ties1887/Mesh-radio-Halow-LoRa/images/345634.jpeg

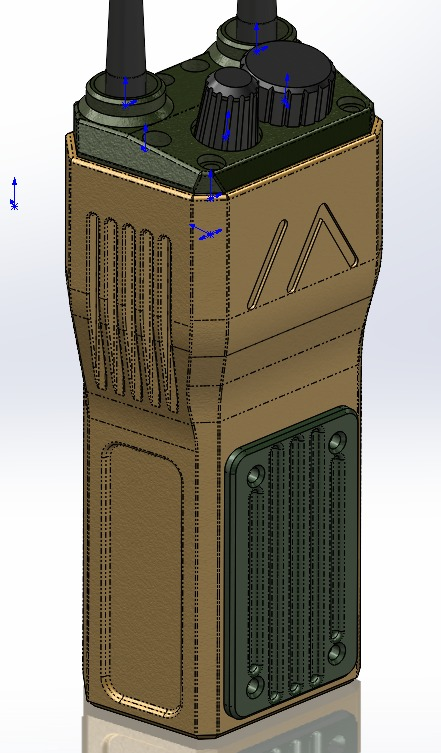
images/345634.jpeg
