ties1887/Mesh-radio-Halow-LoRa/images/2345235.jpeg

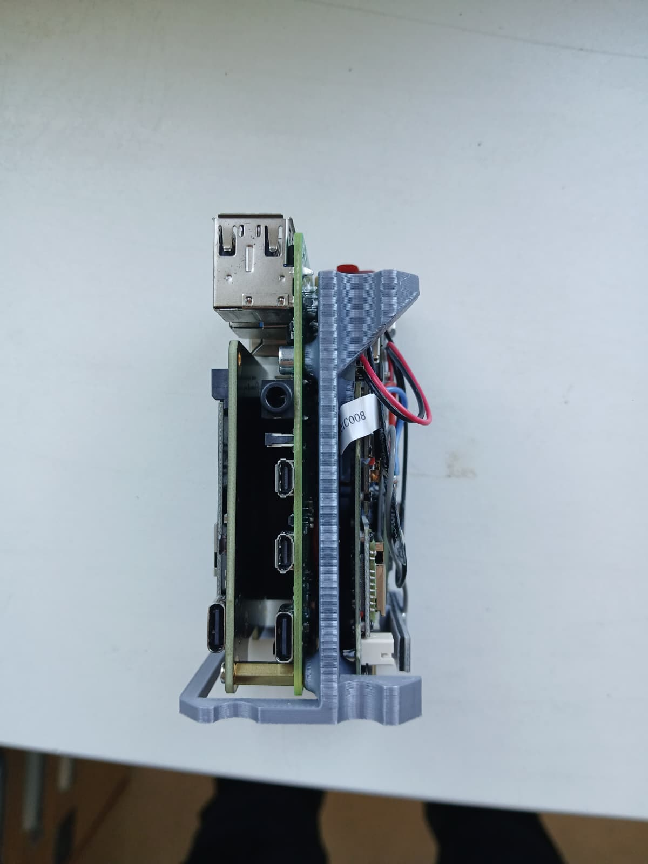
images/2345235.jpeg
