ties1887/Mesh-radio-Halow-LoRa/images/7345634.jpeg

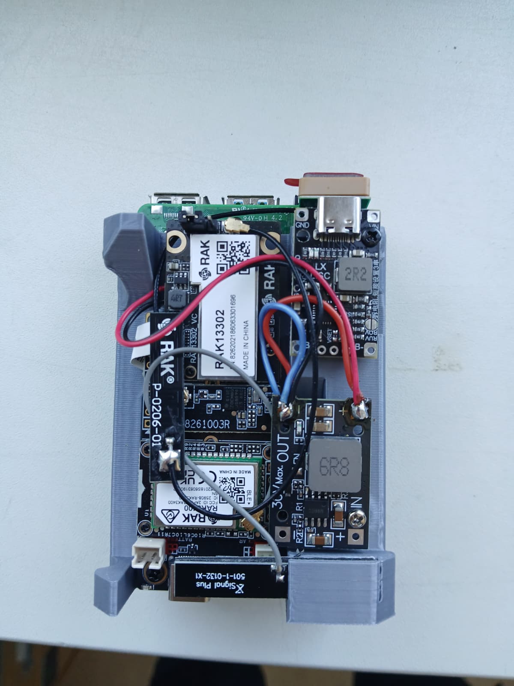
images/7345634.jpeg
