ties1887/Mesh-radio-Halow-LoRa/images/23452345.png

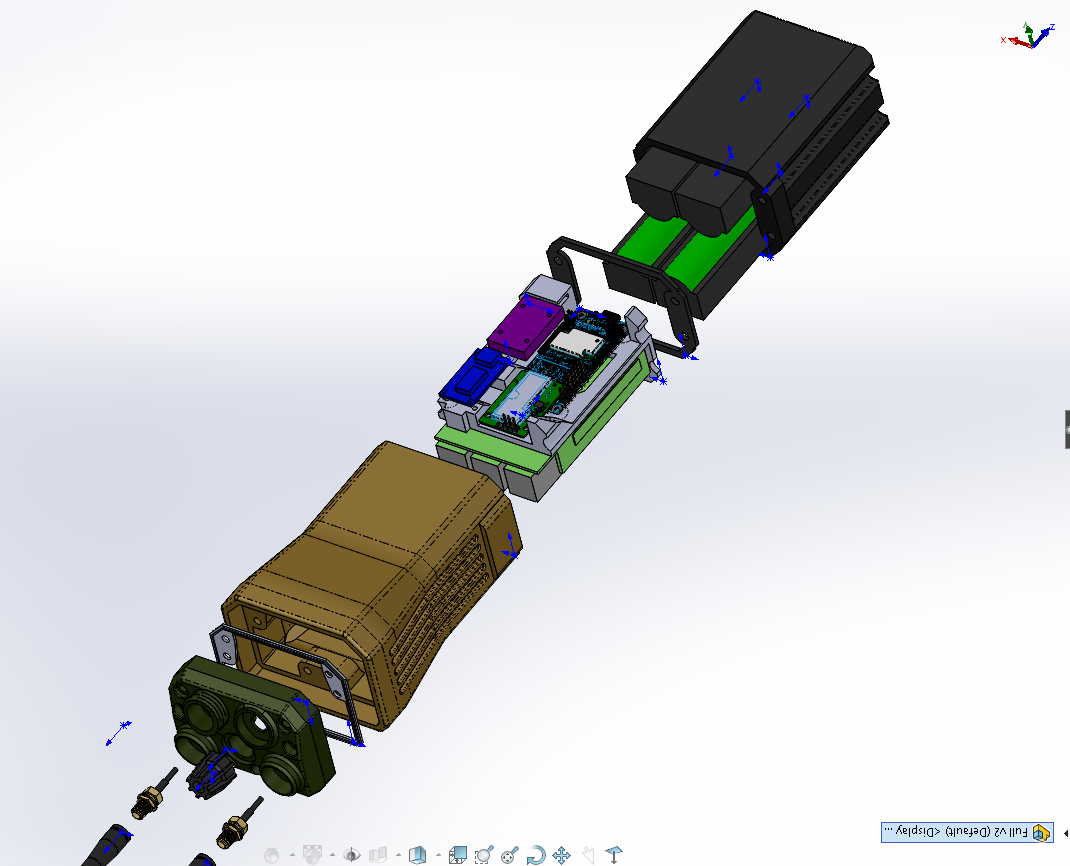
images/23452345.png
