ties1887/Mesh-radio-Halow-LoRa/images/45674567.jpeg

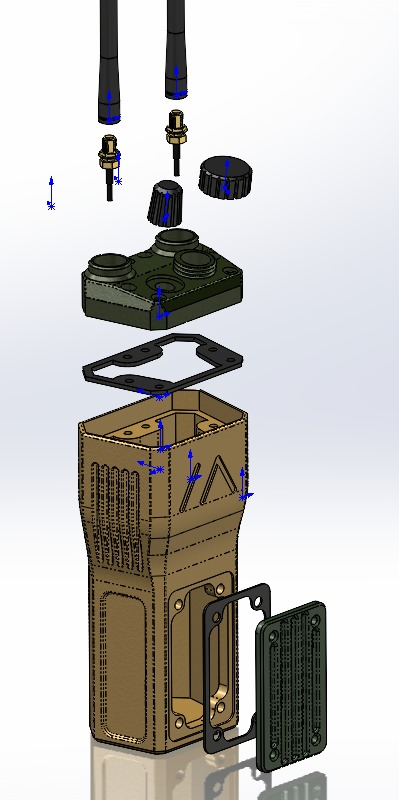
images/45674567.jpeg
