ties1887/Mesh-radio-Halow-LoRa/images/645737645.jpeg

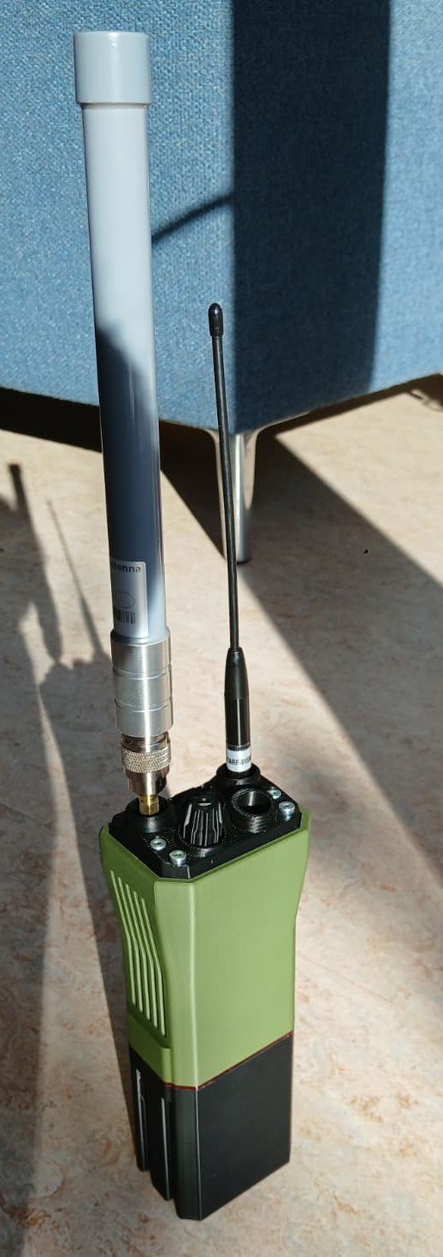
images/645737645.jpeg
