ties1887/Mesh-radio-Halow-LoRa/images/654745745.jpeg

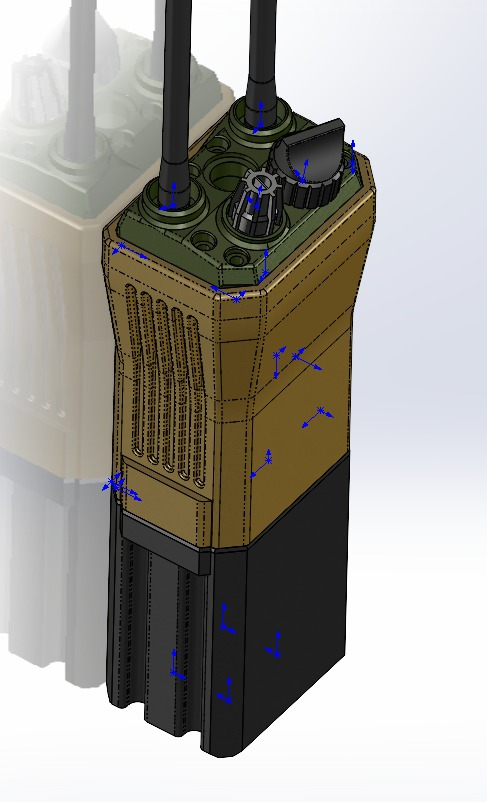
images/654745745.jpeg
