ties1887/Mesh-radio-Halow-LoRa/images/765474657.png

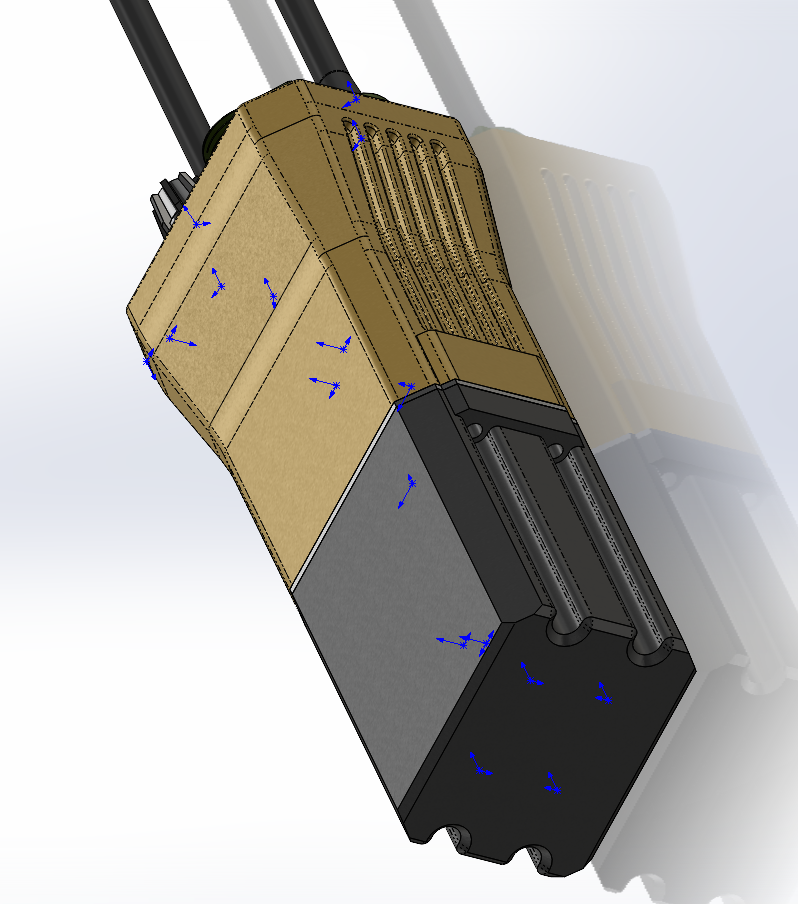
images/765474657.png
