ties1887/Mesh-radio-Halow-LoRa/images/2436436325.png

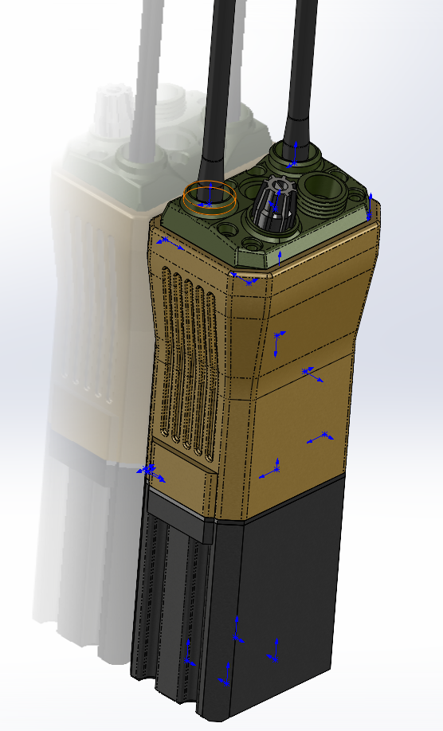
images/2436436325.png
