ties1887/Mesh-radio-Halow-LoRa/images/3456345634.jpeg

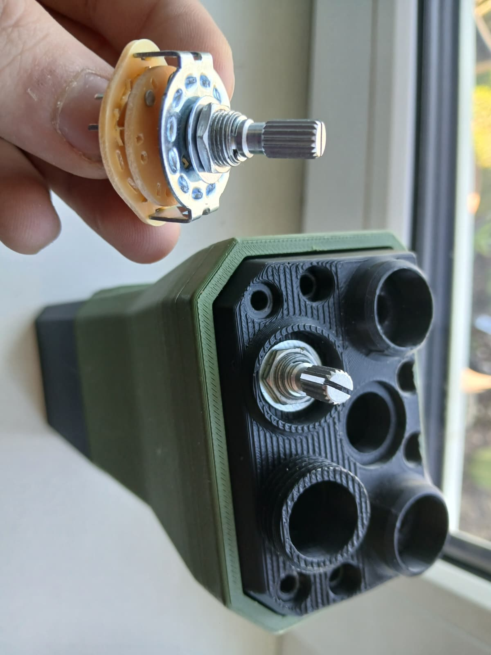
images/3456345634.jpeg
