ties1887/Mesh-radio-Halow-LoRa/images/3456346346.png

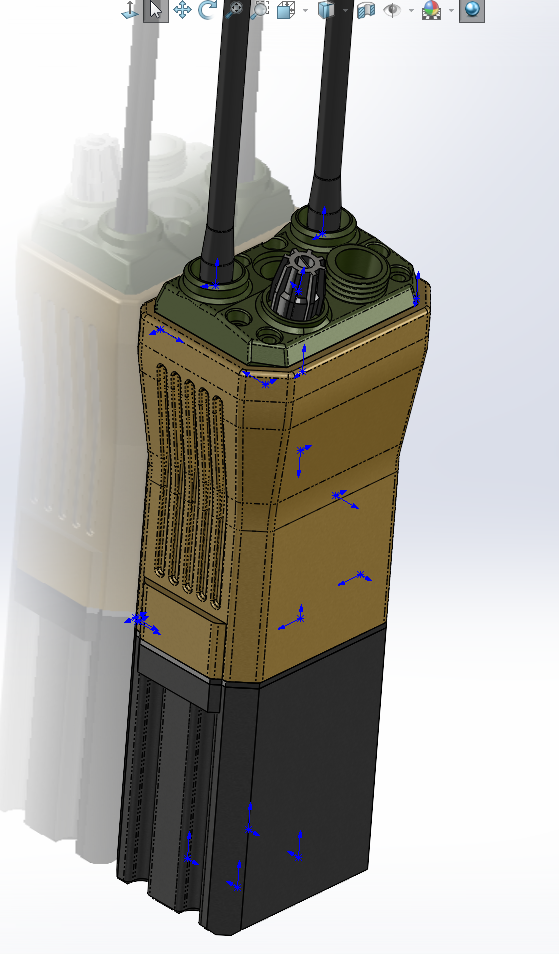
images/3456346346.png
