ties1887/Mesh-radio-Halow-LoRa/images/3456765437.png

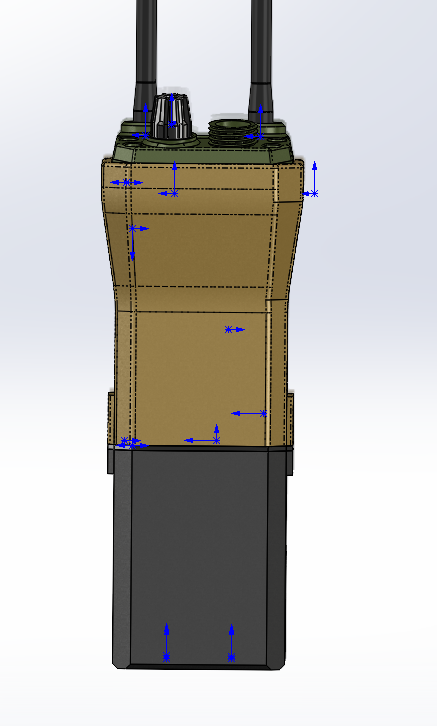
images/3456765437.png
