ties1887/Mesh-radio-Halow-LoRa/images/4567457457.jpeg

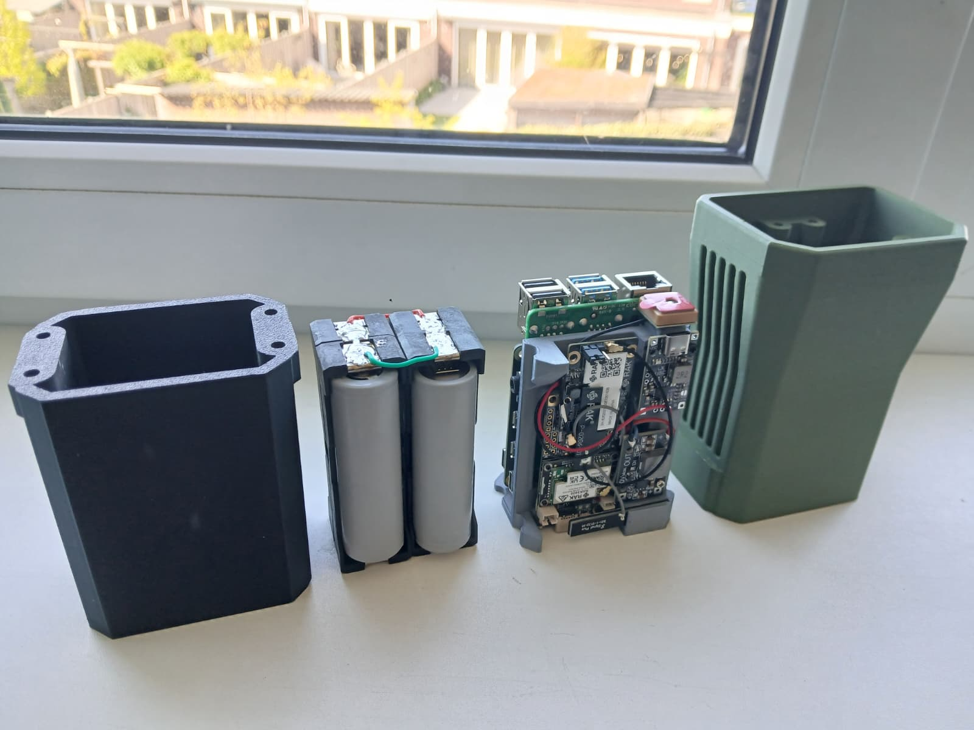
images/4567457457.jpeg
