ties1887/Mesh-radio-Halow-LoRa/images/7686587568.jpeg

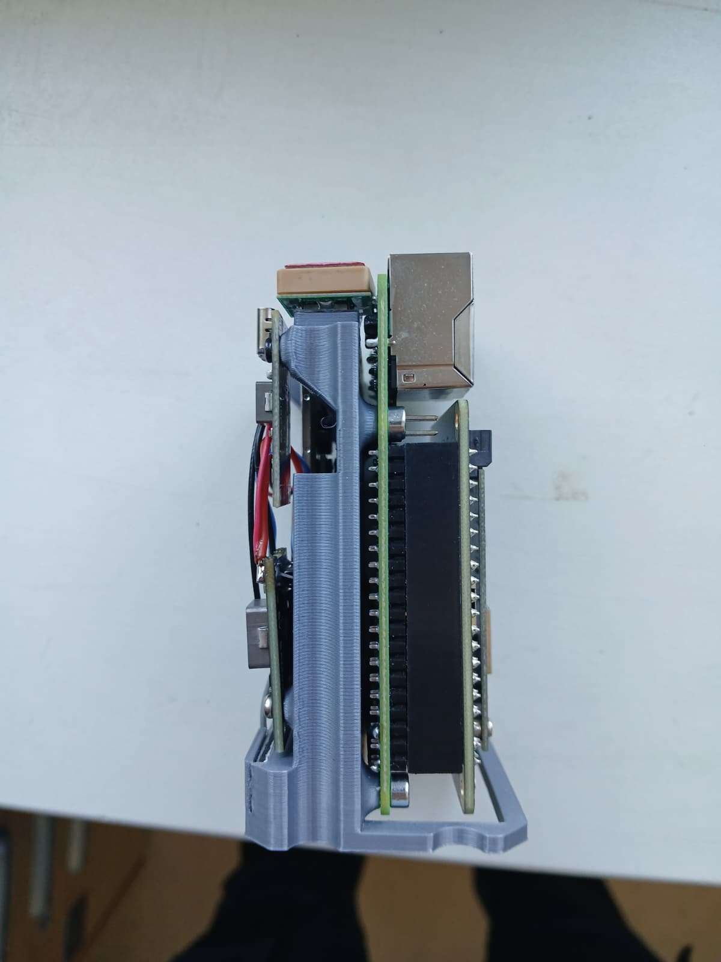
images/7686587568.jpeg
