ties1887/Mesh-radio-Halow-LoRa/images/45674567457.jpeg

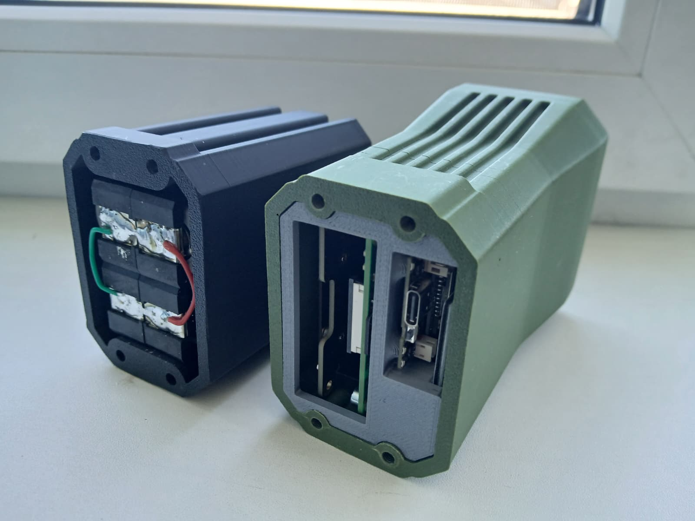
images/45674567457.jpeg
