ties1887/Mesh-radio-Halow-LoRa/images/45674567457.png

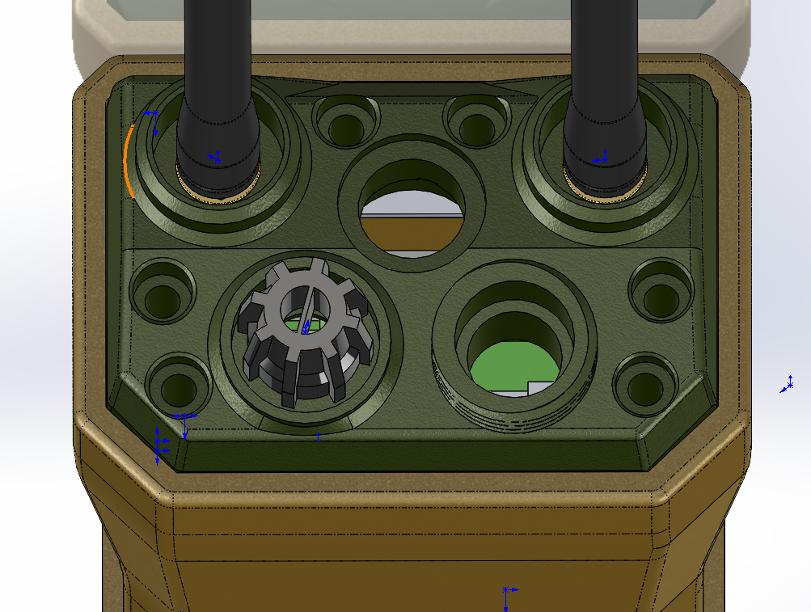
images/45674567457.png
