ties1887/Mesh-radio-Halow-LoRa/images/54674567457.jpeg

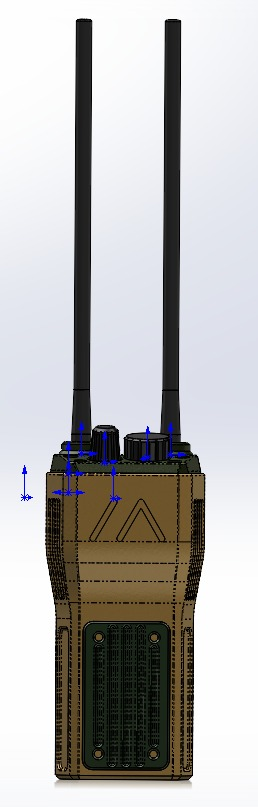
images/54674567457.jpeg
