ties1887/Mesh-radio-Halow-LoRa/images/64574567456.jpeg

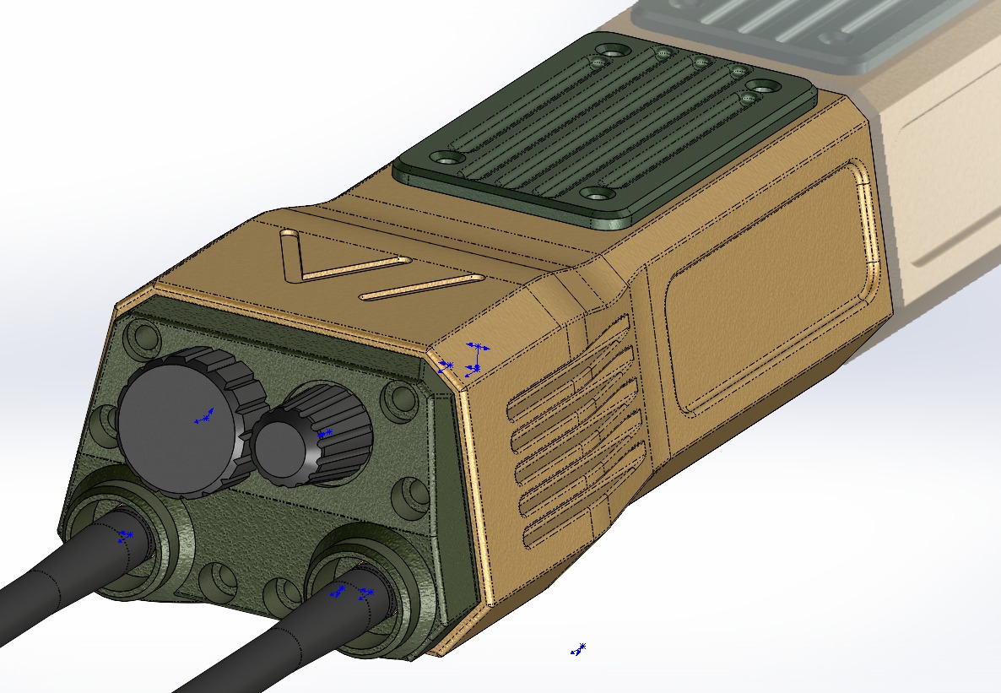
images/64574567456.jpeg
