ties1887/Mesh-radio-Halow-LoRa/images/75688568756.png

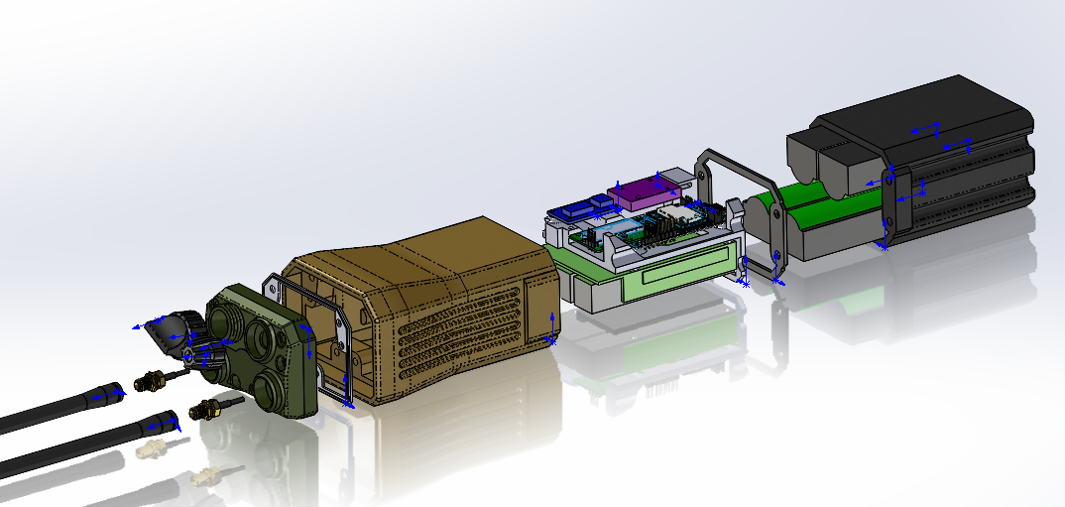
images/75688568756.png
