ties1887/Mesh-radio-Halow-LoRa/images/435634643643.jpeg

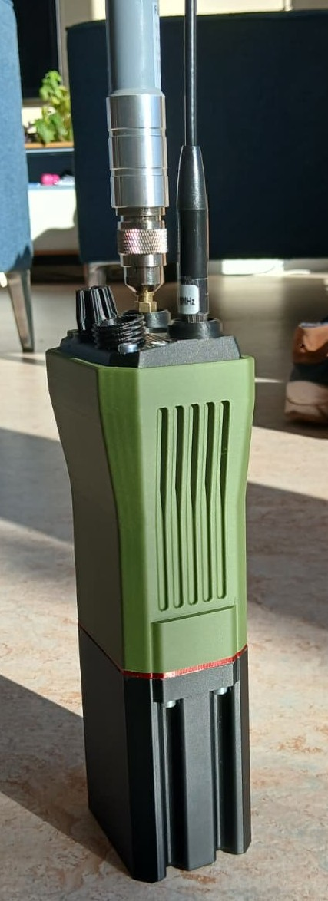
images/435634643643.jpeg
