ties1887/Mesh-radio-Halow-LoRa/images/567856785678.jpeg

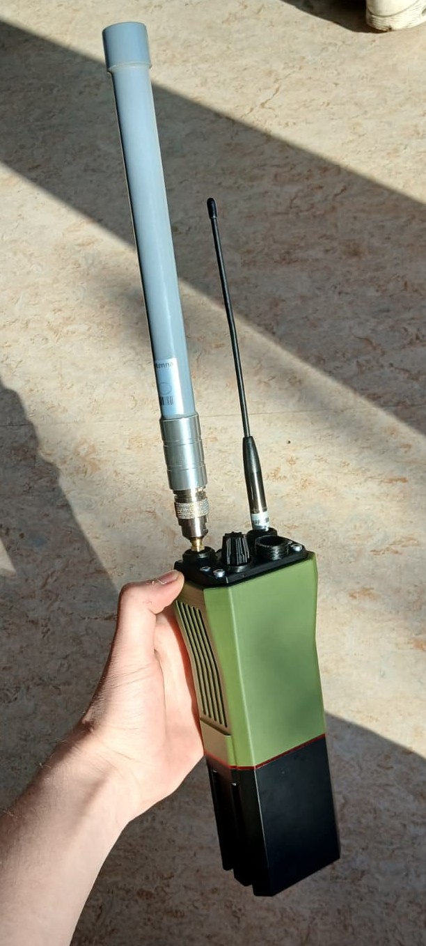
images/567856785678.jpeg
