ties1887/Mesh-radio-Halow-LoRa/images/765476547456.jpeg

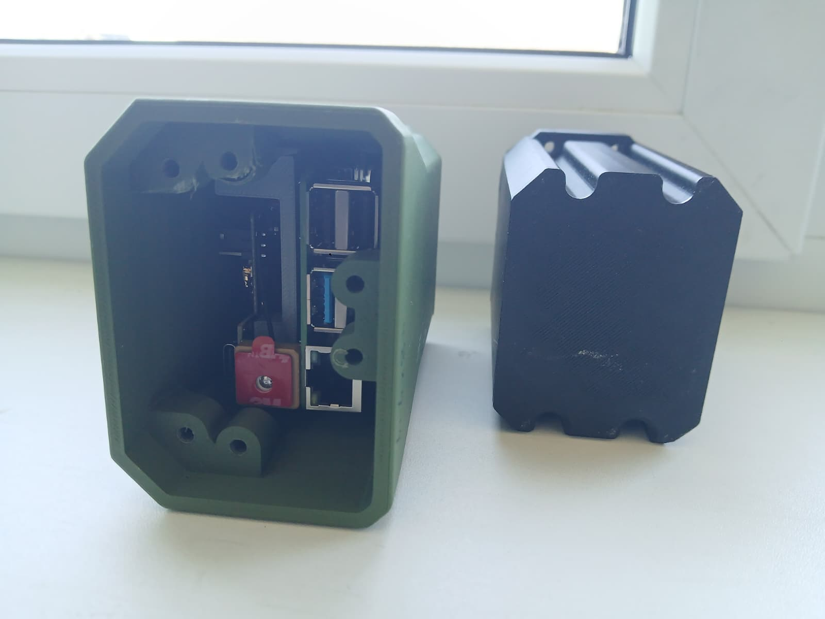
images/765476547456.jpeg
