ties1887/Mesh-radio-Halow-LoRa/images/3456345634634.jpeg

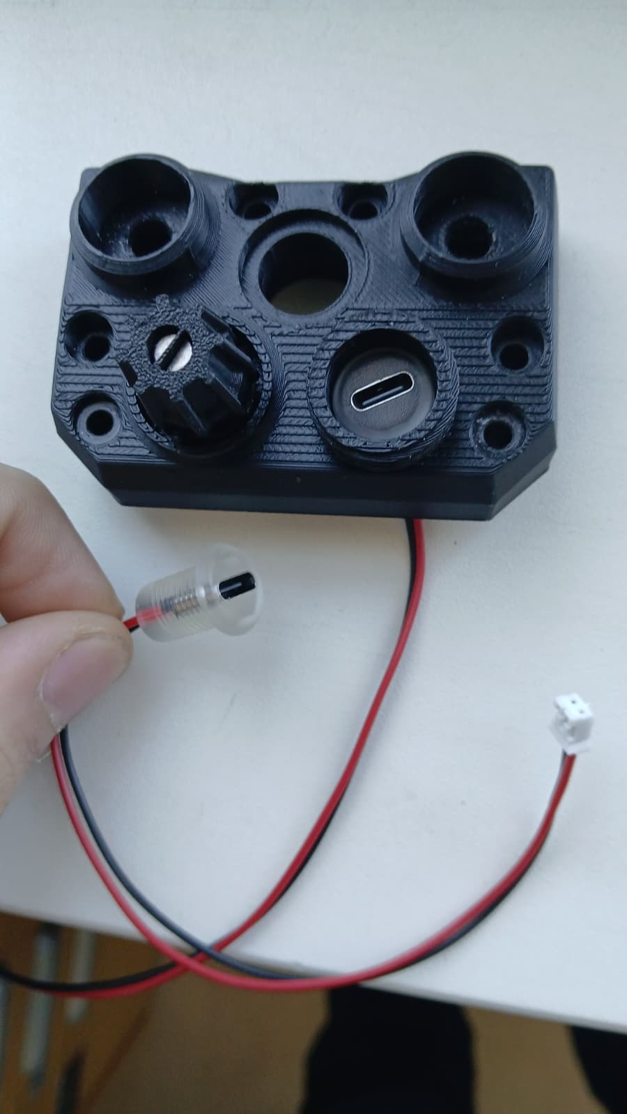
images/3456345634634.jpeg
