ties1887/Mesh-radio-Halow-LoRa/images/45674567435754.jpeg

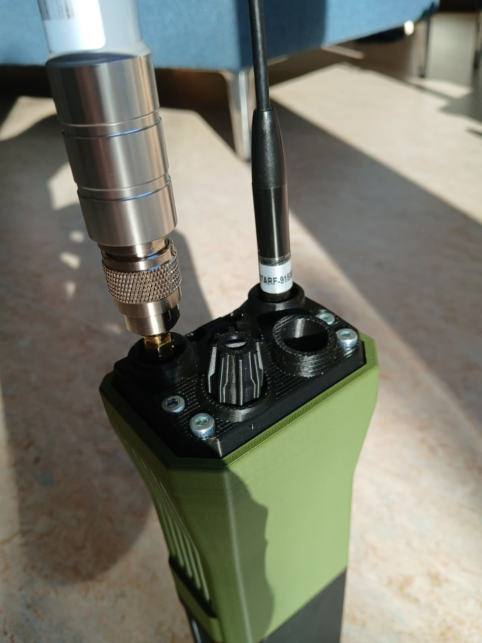
images/45674567435754.jpeg
