ties1887/Mesh-radio-Halow-LoRa/images/Schermafbeelding 2026-08-16 174457.png

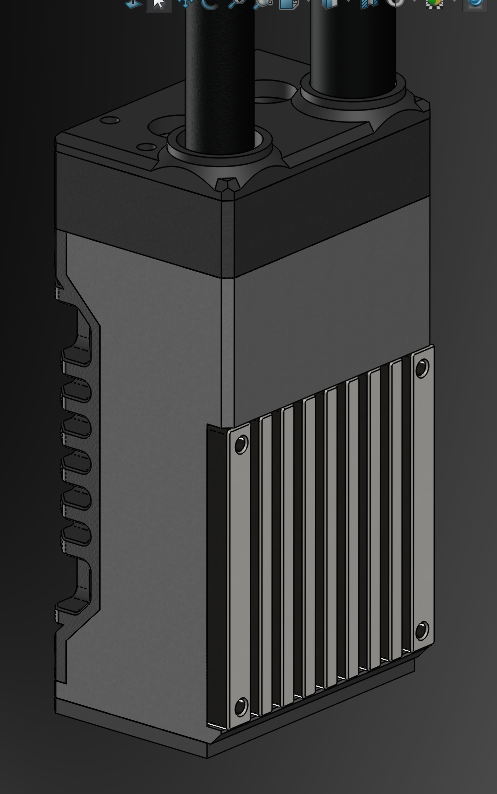
images/Schermafbeelding 2026-08-16 174457.png
