ties1887/Mesh-radio-Halow-LoRa/images/Schermafbeelding 2026-08-16 174508.png

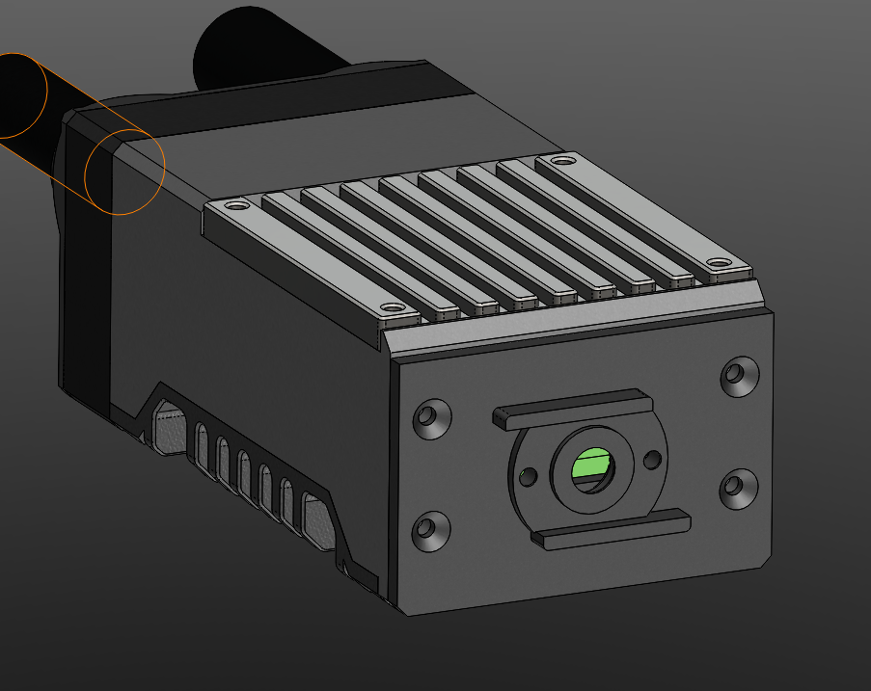
images/Schermafbeelding 2026-08-16 174508.png
