ties1887/Mesh-radio-Halow-LoRa/images/WhatsApp Image 2026-06-27 at 20.04.40.jpeg

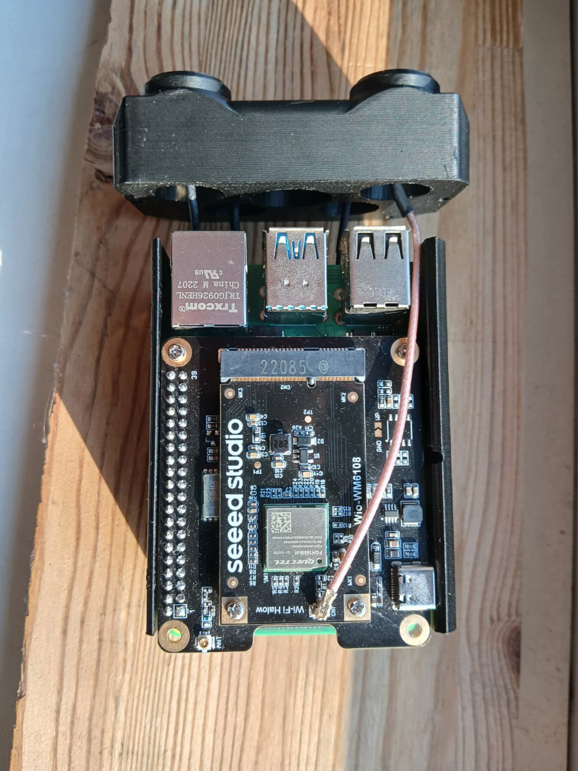
images/WhatsApp Image 2026-06-27 at 20.04.40.jpeg
