ties1887/Mesh-radio-Halow-LoRa/Twist-Lock-Battery-Pack/STL/Battery_Twist_Lock_Pack.SLDASM - Twist_Lock_Wing-1.STL

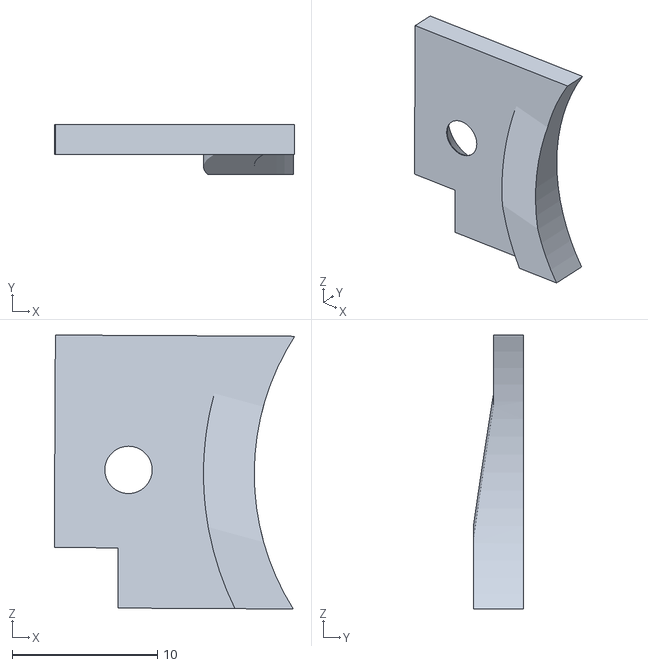
[picture p44: CAD file, 2026-08-21]
Twist-Lock-Battery-Pack/STL/Battery_Twist_Lock_Pack.SLDASM - Twist_Lock_Wing-1.STL
16.6 x 3.48 x 18.9
