ties1887/Mesh-radio-Halow-LoRa/Twist-Lock-Battery-Pack/STL/Battery_Twist_Lock_Pack.SLDASM - Battery_pin_Contact-1.STL

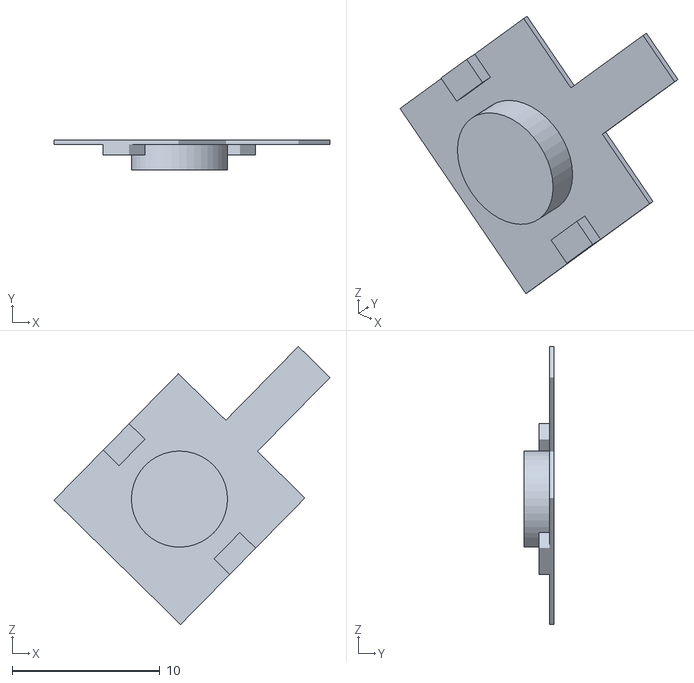
[picture p45: CAD file, 2026-08-21]
Twist-Lock-Battery-Pack/STL/Battery_Twist_Lock_Pack.SLDASM - Battery_pin_Contact-1.STL
18.7 x 2.00 x 18.8
