ties1887/Mesh-radio-Halow-LoRa/Twist-Lock-Battery-Pack/STL/Battery_Twist_Lock_Pack.SLDASM - Twist lock battery part V3-1.STL

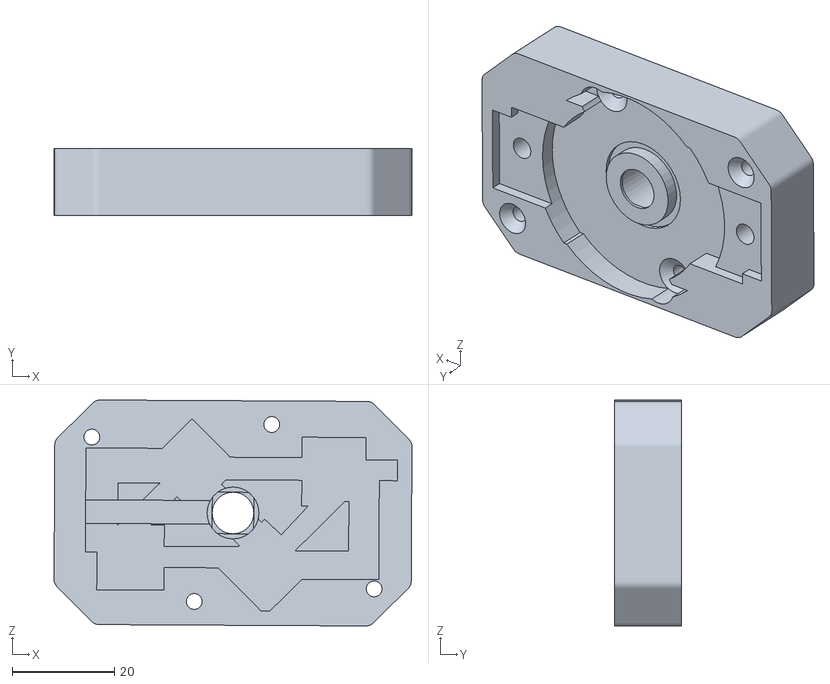
[picture p46: CAD file, 2026-08-21]
Twist-Lock-Battery-Pack/STL/Battery_Twist_Lock_Pack.SLDASM - Twist lock battery part V3-1.STL
70.1 x 13.1 x 44.3
