ties1887/Mesh-radio-Halow-LoRa/First-Generation-Builds/Standalone-Lunpid-enclosure/3MF/enclosure.3MF

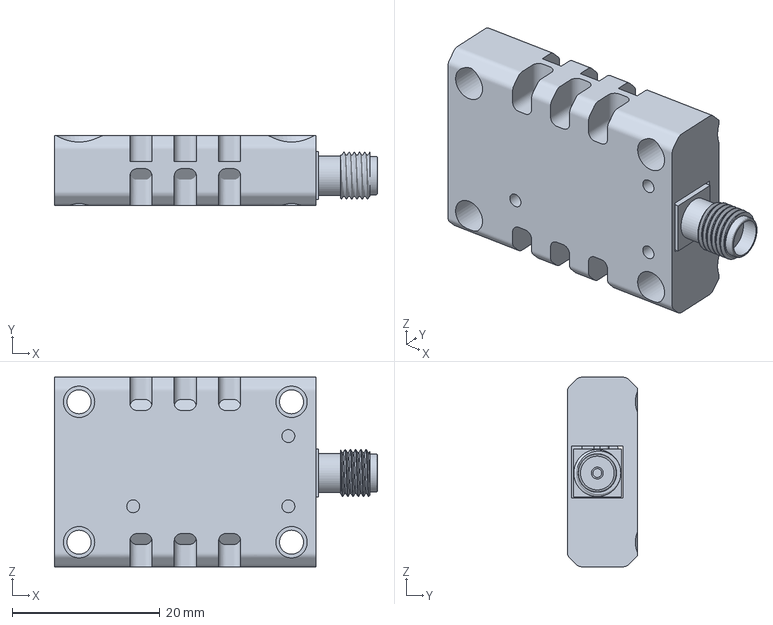
[picture p47: CAD file, 2026-07-13]
First-Generation-Builds/Standalone-Lunpid-enclosure/3MF/enclosure.3MF
43.7 x 9.50 x 25.6 mm
