ties1887/Mesh-radio-Halow-LoRa/First-Generation-Builds/Standalone-Lunpid-enclosure/Solidworks 2025/lunpid_longwave_v0.1.step

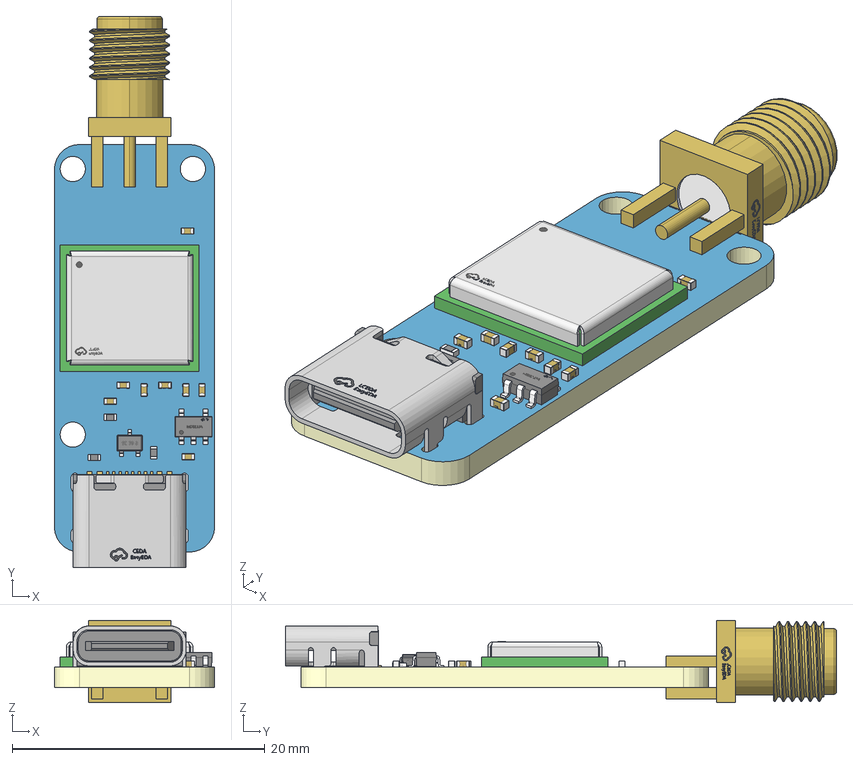
[picture p49: CAD file, 2026-07-13]
First-Generation-Builds/Standalone-Lunpid-enclosure/Solidworks 2025/lunpid_longwave_v0.1.step
12.7 x 43.6 x 6.50 mm
Board~8fiY
TopCopper~8fiY
BottomCopper~8fiY
TopSilkscreen~8fiY
BottomSilkscreen~8fiY
TopFpcStiffener~8fiY
BottomFpcStiffener~8fiY
SOT-23-5_L2.9-W1.6-P0.95-LS2.8-BL~SOT-23-5_ L2.9-W1.6-P0.95-LS2.8-BL~8fiY
R0402~C0402_L1.0-W0.5-H0.5~8fiY x 8
R0402~R0402_L1.0-W0.5-H0.4~8fiY x 3
SMA-SMD_BWSMA-KE-P001~SMA-TH_5P-L6.5-W6.5-H9.5_BWSMA-KE-P001~8fiY
SC-70-3_L2.0-W1.3-P0.65-LS2.1-BL~SC-70-3_L2.0-W1.3-P0.65-LS2.1-BL~8fiY
LGA-38_L11.0-W10.0-P1.00-TL~LGA-38_L11.0-W10.0-P1.00-TL~8fiY
USB-C-SMD_TYPE-C-6PIN-2MD-073~USB-C-SMD_TYPEC-304YDSW-ACP16~8fiY
