ties1887/Mesh-radio-Halow-LoRa/First-Generation-Builds/Standalone-Lunpid-enclosure/STEP/Top part.STEP

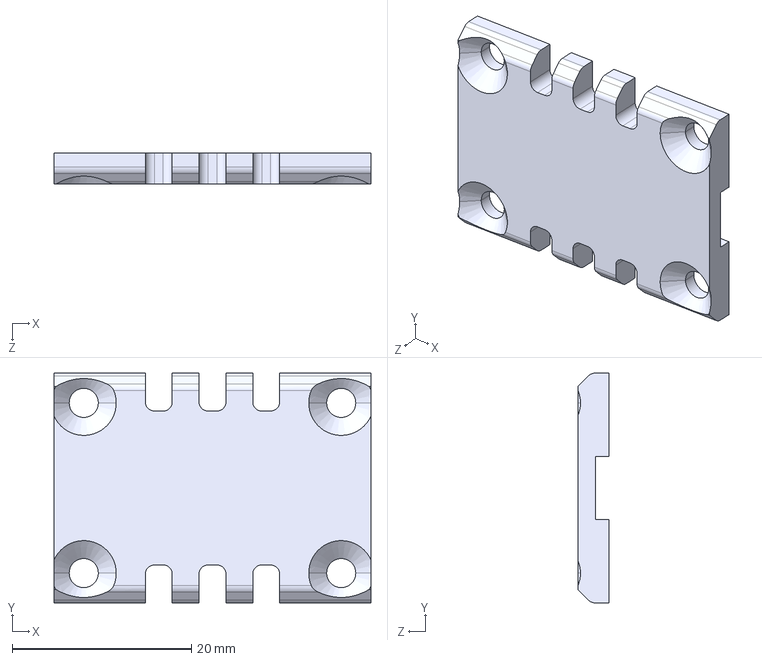
[picture p50: CAD file, 2026-07-13]
First-Generation-Builds/Standalone-Lunpid-enclosure/STEP/Top part.STEP
35.4 x 25.7 x 3.50 mm
