ties1887/Mesh-radio-Halow-LoRa/First-Generation-Builds/V2_30-5-2026/Solidworks 2023/base.SLDPRT

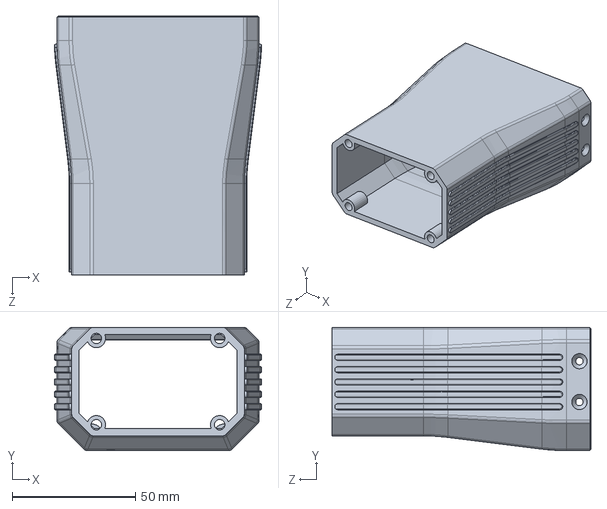
[picture p51: CAD file, 2026-05-30]
First-Generation-Builds/V2_30-5-2026/Solidworks 2023/base.SLDPRT
84.0 x 50.0 x 105.0 mm
