ties1887/Mesh-radio-Halow-LoRa/First-Generation-Builds/V2_30-5-2026/Solidworks 2025/middel part.SLDPRT

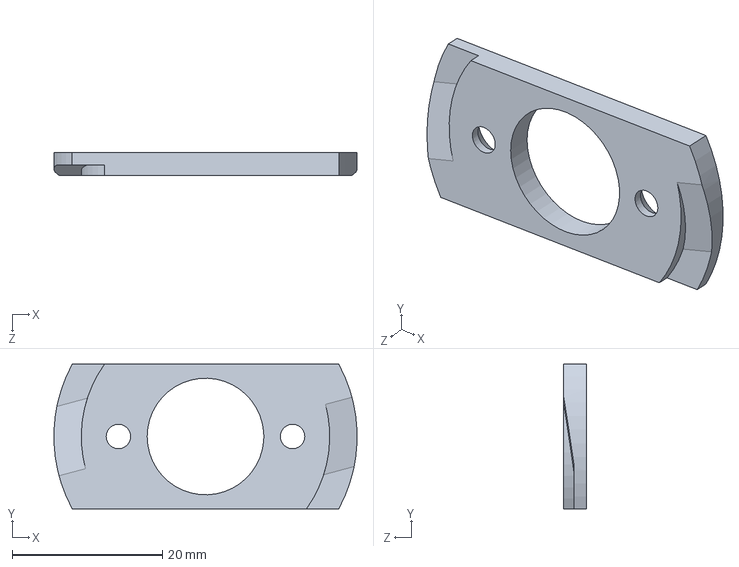
[picture p52: CAD file, 2026-05-30]
First-Generation-Builds/V2_30-5-2026/Solidworks 2025/middel part.SLDPRT
40.4 x 19.3 x 3.00 mm
