ties1887/Mesh-radio-Halow-LoRa/First-Generation-Builds/V2_30-5-2026/step/PCB frame.STEP

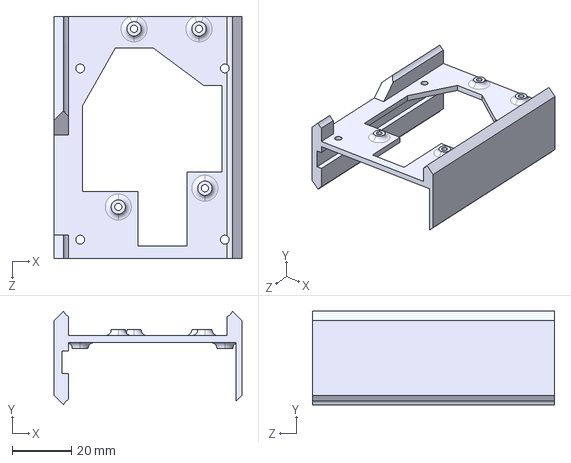
[picture p53: CAD file, 2026-05-30]
First-Generation-Builds/V2_30-5-2026/step/PCB frame.STEP
63.6 x 31.7 x 82.0 mm
