ties1887/Mesh-radio-Halow-LoRa/First-Generation-Builds/V2_30-5-2026/STL/Assem2 - top-1.STL

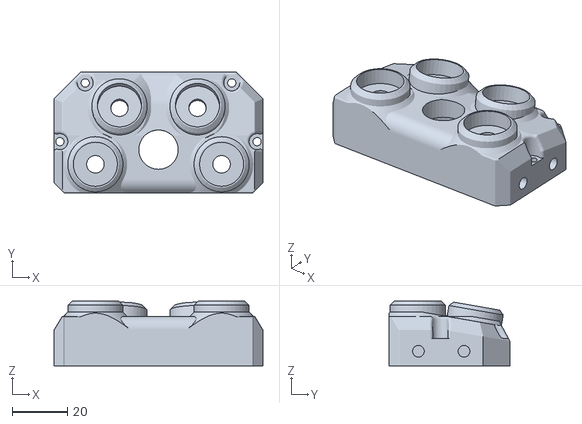
[picture p54: CAD file, 2026-05-31]
First-Generation-Builds/V2_30-5-2026/STL/Assem2 - top-1.STL
75.8 x 43.8 x 23.5
