ties1887/Mesh-radio-Halow-LoRa/First-Generation-Builds/V3_18-6-2026/Solidworks 2023/Part1.SLDPRT

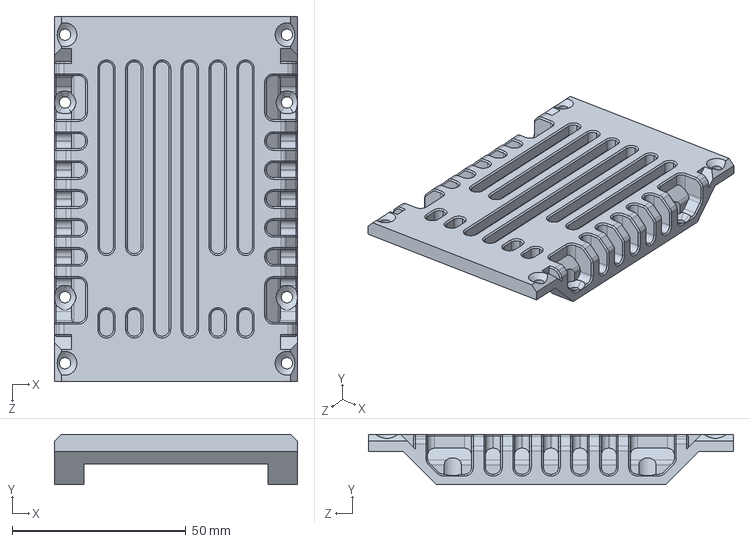
[picture p55: CAD file, 2026-06-18]
First-Generation-Builds/V3_18-6-2026/Solidworks 2023/Part1.SLDPRT
70.0 x 14.5 x 105.0 mm
