ties1887/Mesh-radio-Halow-LoRa/First-Generation-Builds/V3_18-6-2026/Solidworks 2025/Top new.SLDPRT

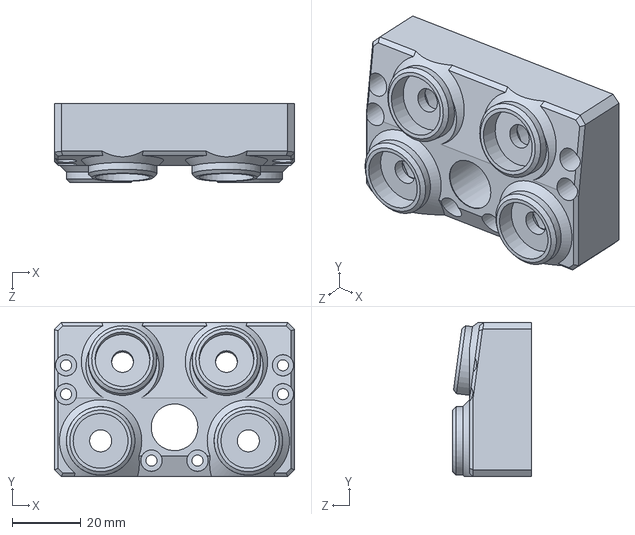
[picture p56: CAD file, 2026-06-18]
First-Generation-Builds/V3_18-6-2026/Solidworks 2025/Top new.SLDPRT
70.0 x 45.0 x 23.0 mm
