ties1887/Mesh-radio-Halow-LoRa/First-Generation-Builds/V3_18-6-2026/STEP/wing part.STEP

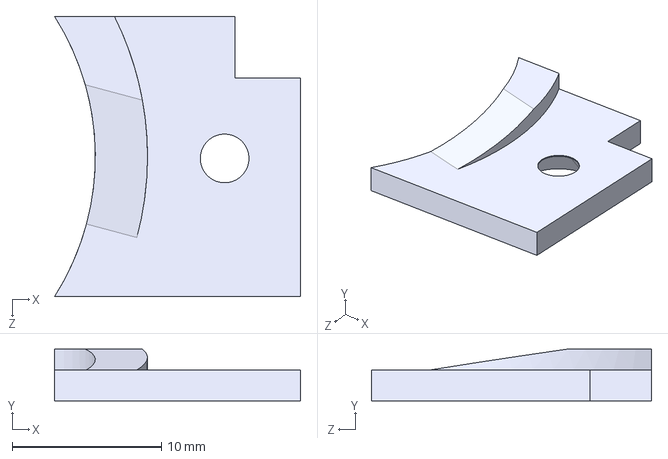
[picture p57: CAD file, 2026-06-18]
First-Generation-Builds/V3_18-6-2026/STEP/wing part.STEP
16.5 x 3.48 x 18.8 mm
