ties1887/Mesh-radio-Halow-LoRa/Second-Generation-Builds/CM4-Carrier-Board/models/DF40HC_3.0_100DS.stp

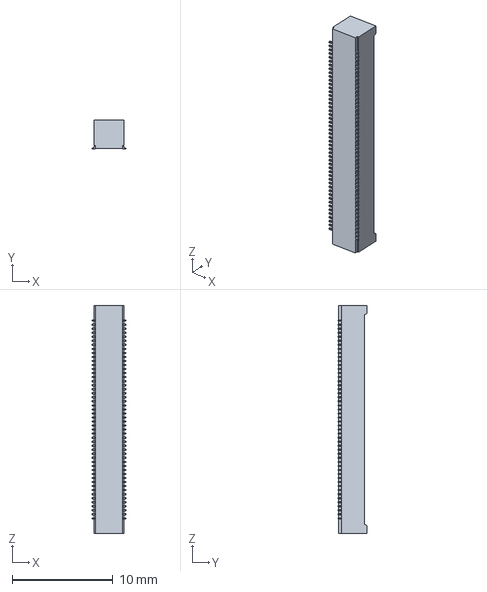
[picture p58: CAD file, 2026-09-19]
Second-Generation-Builds/CM4-Carrier-Board/models/DF40HC_3.0_100DS.stp
3.38 x 2.90 x 22.6 mm
