ties1887/Mesh-radio-Halow-LoRa/Second-Generation-Builds/P4-Wio/3MF/P4-WIO_v1.1.3MF

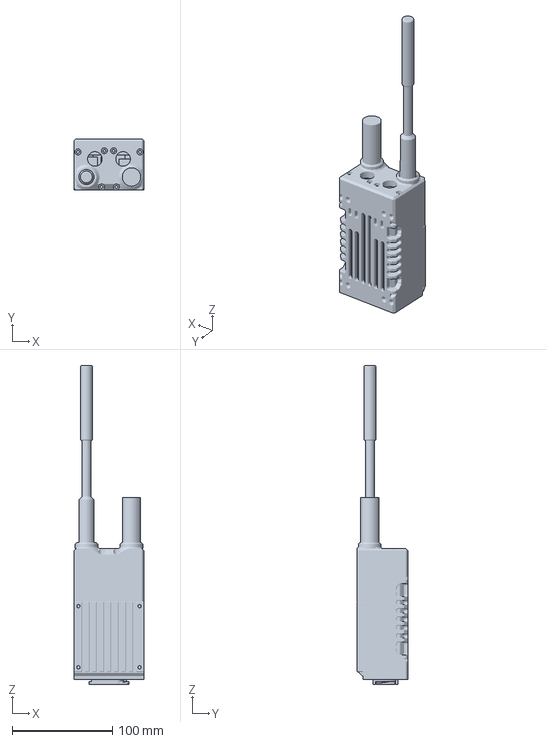
[picture p59: CAD file, 2026-08-21]
Second-Generation-Builds/P4-Wio/3MF/P4-WIO_v1.1.3MF
70.0 x 51.0 x 318.7 mm
