ties1887/Mesh-radio-Halow-LoRa/Second-Generation-Builds/P4-Wio/STEP/enclosure_top_cover.STEP

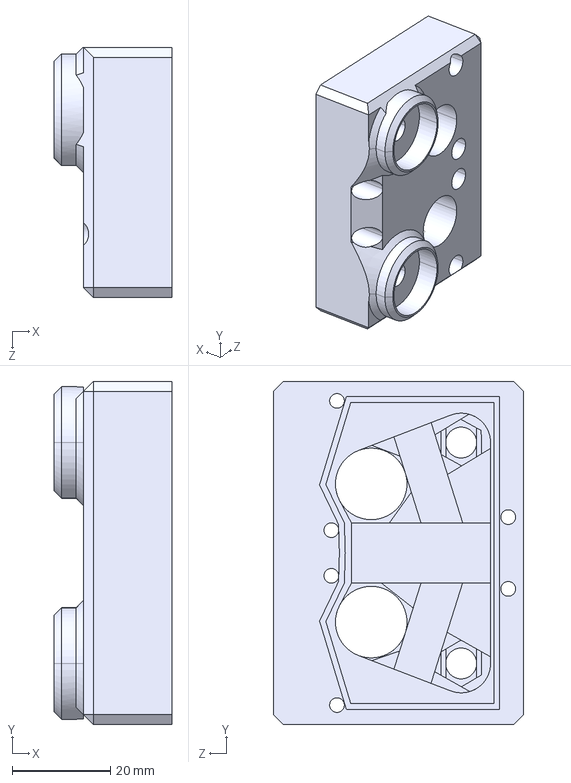
[picture p60: CAD file, 2026-08-21]
Second-Generation-Builds/P4-Wio/STEP/enclosure_top_cover.STEP
24.0 x 70.0 x 51.0 mm
