ties1887/Mesh-radio-Halow-LoRa/First-Generation-Builds/Standalone-Lunpid-enclosure/Solidworks 2025/Bottom part.SLDPRT

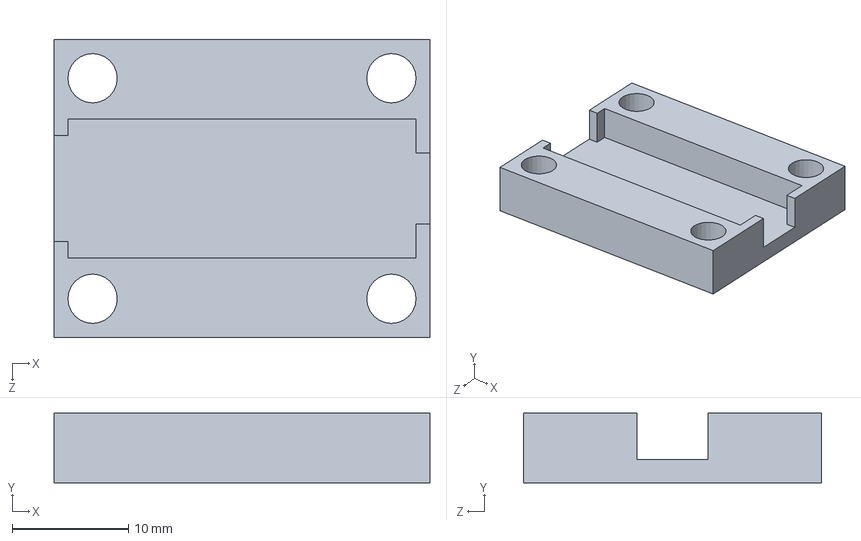
[picture p61: CAD file, 2026-07-13]
First-Generation-Builds/Standalone-Lunpid-enclosure/Solidworks 2025/Bottom part.SLDPRT
32.4 x 6.00 x 25.6 mm
