ties1887/Mesh-radio-Halow-LoRa/First-Generation-Builds/V2_30-5-2026/Solidworks 2023/Twist lock radio part V3.SLDPRT

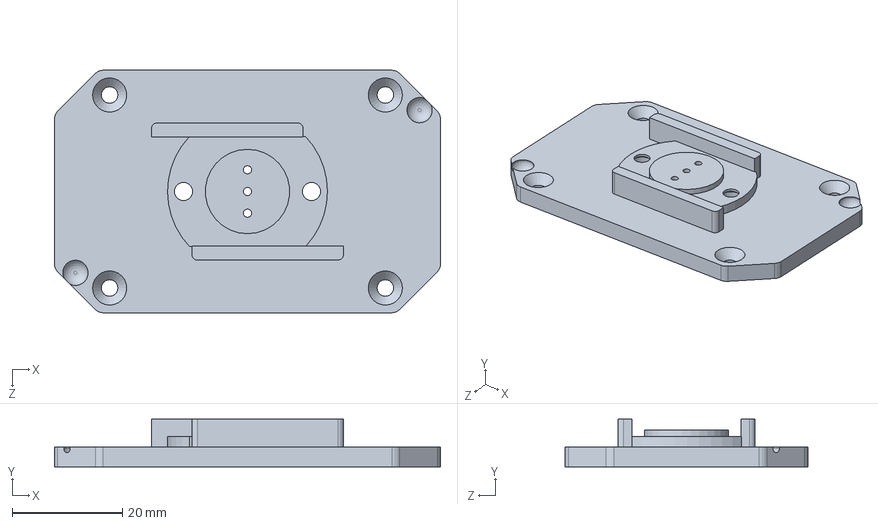
[picture p62: CAD file, 2026-05-30]
First-Generation-Builds/V2_30-5-2026/Solidworks 2023/Twist lock radio part V3.SLDPRT
70.0 x 8.68 x 44.0 mm
