ties1887/Mesh-radio-Halow-LoRa/First-Generation-Builds/V2_30-5-2026/Solidworks 2025/batcase.SLDPRT

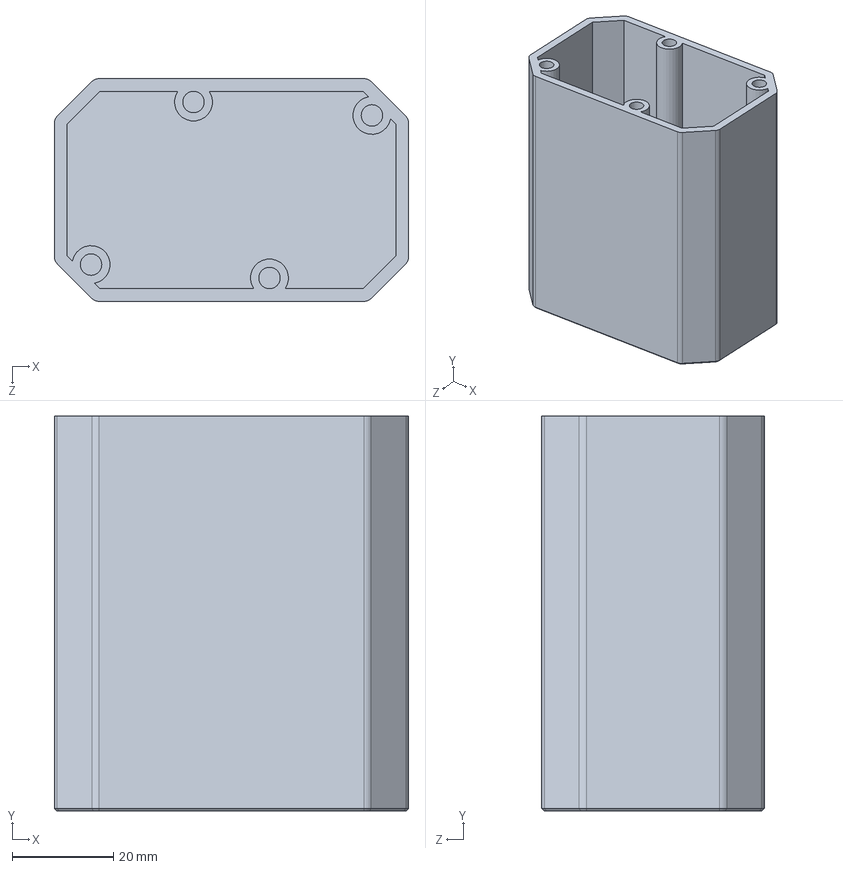
[picture p63: CAD file, 2026-05-30]
First-Generation-Builds/V2_30-5-2026/Solidworks 2025/batcase.SLDPRT
70.0 x 78.0 x 44.0 mm
