ties1887/Mesh-radio-Halow-LoRa/First-Generation-Builds/V2_30-5-2026/step/buck converter.STEP

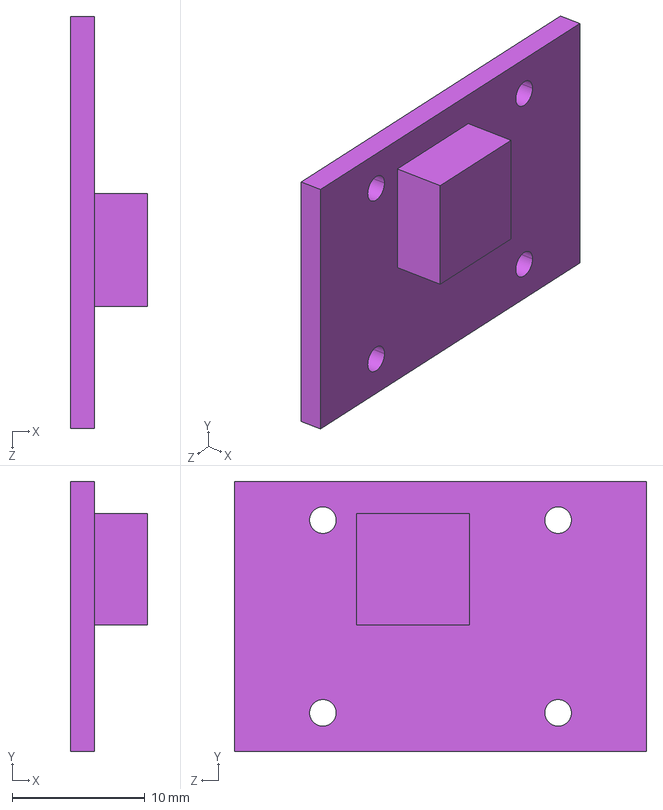
[picture p64: CAD file, 2026-05-30]
First-Generation-Builds/V2_30-5-2026/step/buck converter.STEP
5.80 x 20.4 x 31.0 mm
