ties1887/Mesh-radio-Halow-LoRa/First-Generation-Builds/V2_30-5-2026/STL/Assem2 - Twist lock battery part V3-1.STL

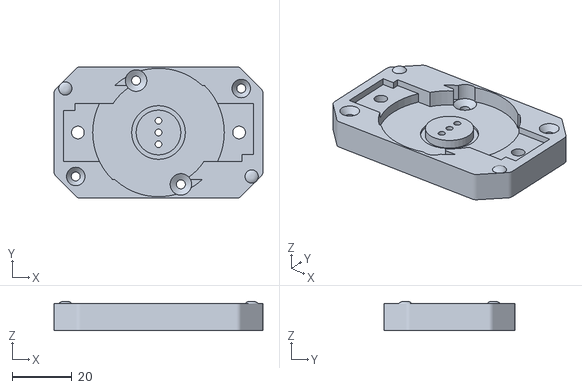
[picture p65: CAD file, 2026-05-31]
First-Generation-Builds/V2_30-5-2026/STL/Assem2 - Twist lock battery part V3-1.STL
70.0 x 44.0 x 9.88
