ties1887/Mesh-radio-Halow-LoRa/Second-Generation-Builds/CM4-Carrier-Board/models/G2401CE.step

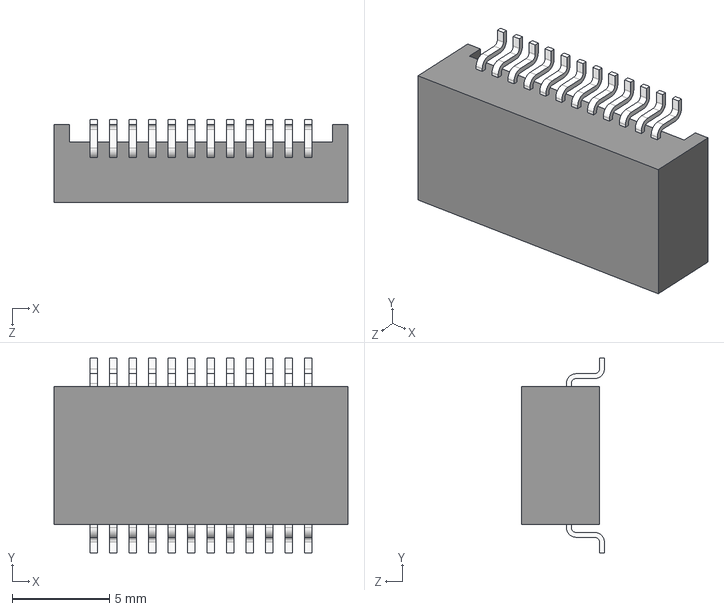
[picture p66: CAD file, 2026-09-19]
Second-Generation-Builds/CM4-Carrier-Board/models/G2401CE.step
15.1 x 10.0 x 4.25 mm
