ties1887/Mesh-radio-Halow-LoRa/Second-Generation-Builds/P4-Wio/STEP/gnns gps.STEP

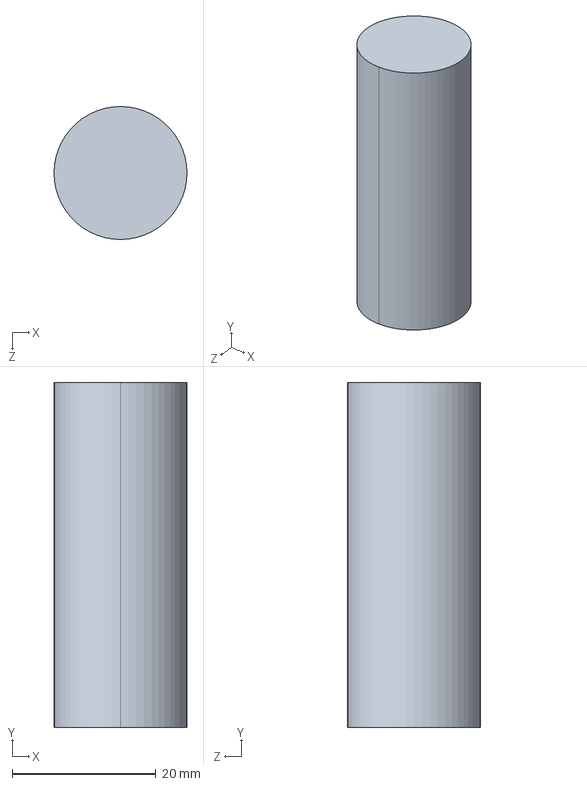
[picture p67: CAD file, 2026-08-21]
Second-Generation-Builds/P4-Wio/STEP/gnns gps.STEP
18.5 x 48.0 x 18.5 mm
