ties1887/Mesh-radio-Halow-LoRa/Twist-Lock-Battery-Pack/STEP/bms 2s.STEP

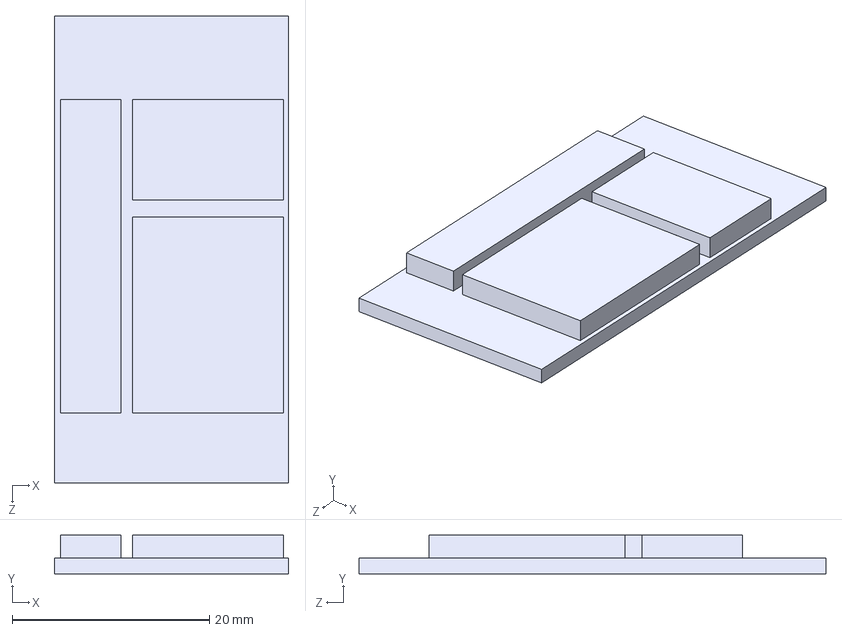
[picture p68: CAD file, 2026-08-21]
Twist-Lock-Battery-Pack/STEP/bms 2s.STEP
23.8 x 3.95 x 47.4 mm
