ties1887/Mesh-radio-Halow-LoRa/First-Generation-Builds/V3_18-6-2026/STEP/pi4withall.STEP

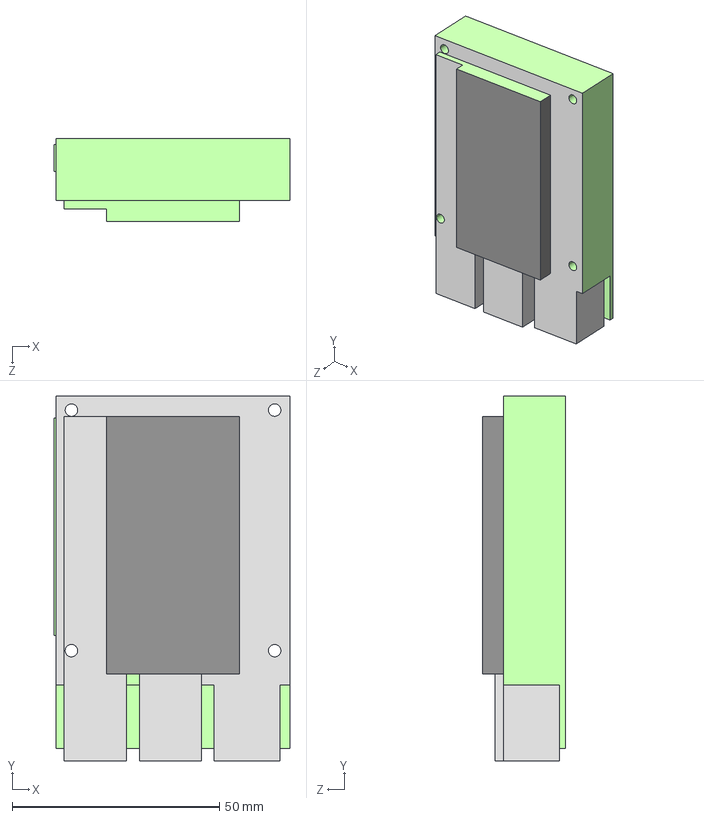
[picture p69: CAD file, 2026-06-18]
First-Generation-Builds/V3_18-6-2026/STEP/pi4withall.STEP
56.8 x 88.0 x 20.0 mm
