ties1887/Mesh-radio-Halow-LoRa/Second-Generation-Builds/CM4-Carrier-Board/models/123A-42E02_C_1.stp

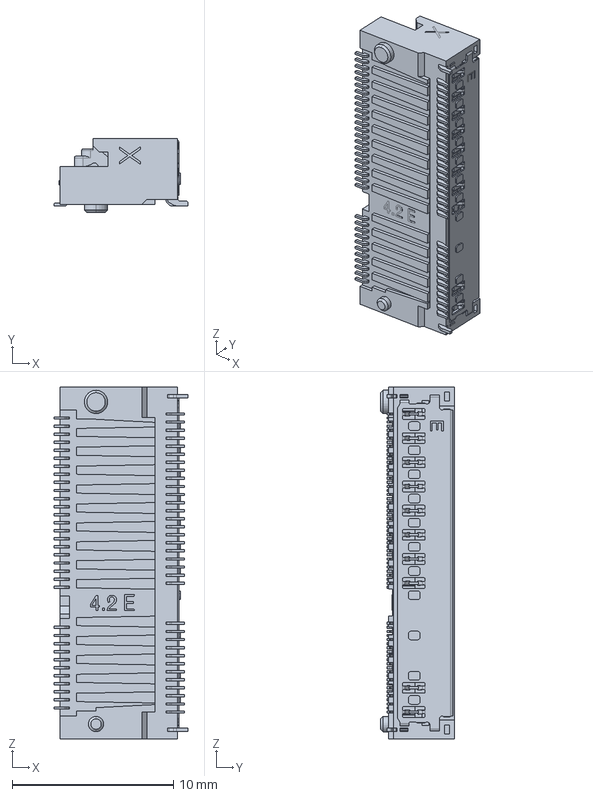
[picture p70: CAD file, 2026-09-19]
Second-Generation-Builds/CM4-Carrier-Board/models/123A-42E02_C_1.stp
8.30 x 4.60 x 21.9 mm
