ties1887/Mesh-radio-Halow-LoRa/Second-Generation-Builds/P4-Wio/STEP/enclosure_front_cover.STEP

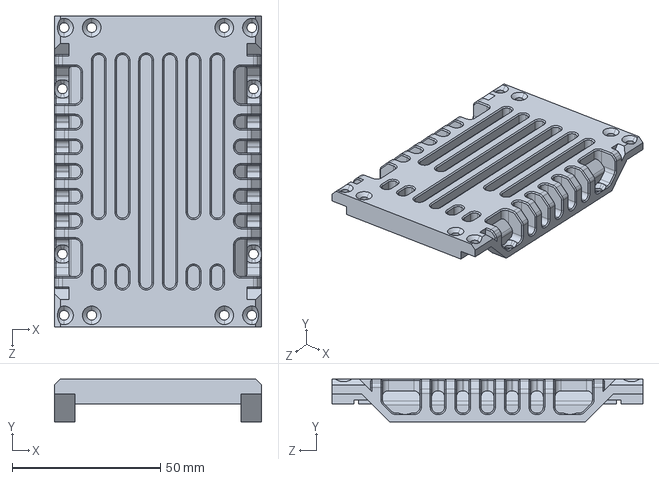
[picture p71: CAD file, 2026-08-21]
Second-Generation-Builds/P4-Wio/STEP/enclosure_front_cover.STEP
70.0 x 14.5 x 105.0 mm
