ties1887/Mesh-radio-Halow-LoRa/First-Generation-Builds/V3_18-6-2026/Solidworks 2025/PCB frame.SLDPRT

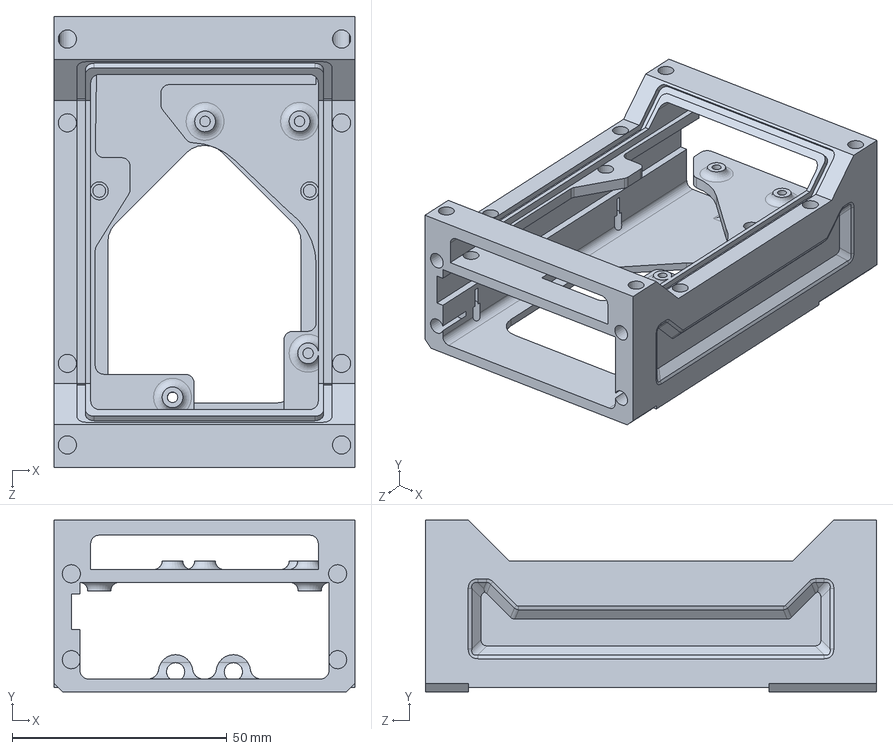
[picture p72: CAD file, 2026-06-18]
First-Generation-Builds/V3_18-6-2026/Solidworks 2025/PCB frame.SLDPRT
70.0 x 40.0 x 105.0 mm
