ties1887/Mesh-radio-Halow-LoRa/First-Generation-Builds/V3_18-6-2026/STEP/Twist lock radio part V3.STEP

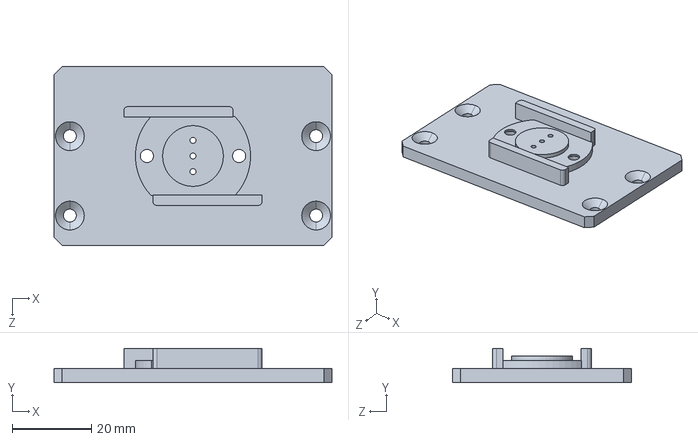
[picture p73: CAD file, 2026-06-18]
First-Generation-Builds/V3_18-6-2026/STEP/Twist lock radio part V3.STEP
70.0 x 8.68 x 45.0 mm
