ties1887/Mesh-radio-Halow-LoRa/Second-Generation-Builds/CM4-Carrier-Board/models/USB2514B_QFN36_6x6.step

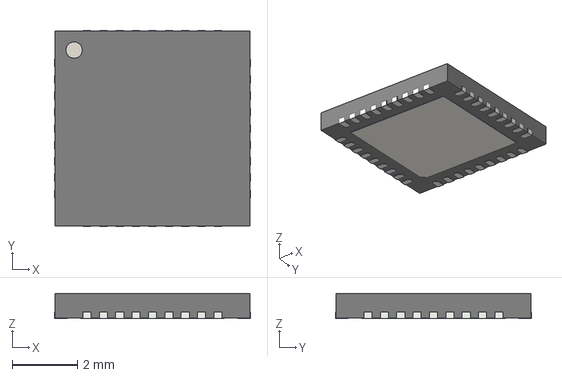
[picture p74: CAD file, 2026-09-19]
Second-Generation-Builds/CM4-Carrier-Board/models/USB2514B_QFN36_6x6.step
6.00 x 6.00 x 0.77 mm
