ties1887/Mesh-radio-Halow-LoRa/Second-Generation-Builds/P4-Wio/STEP/heatsink_external_70x70x3-6mm.STEP

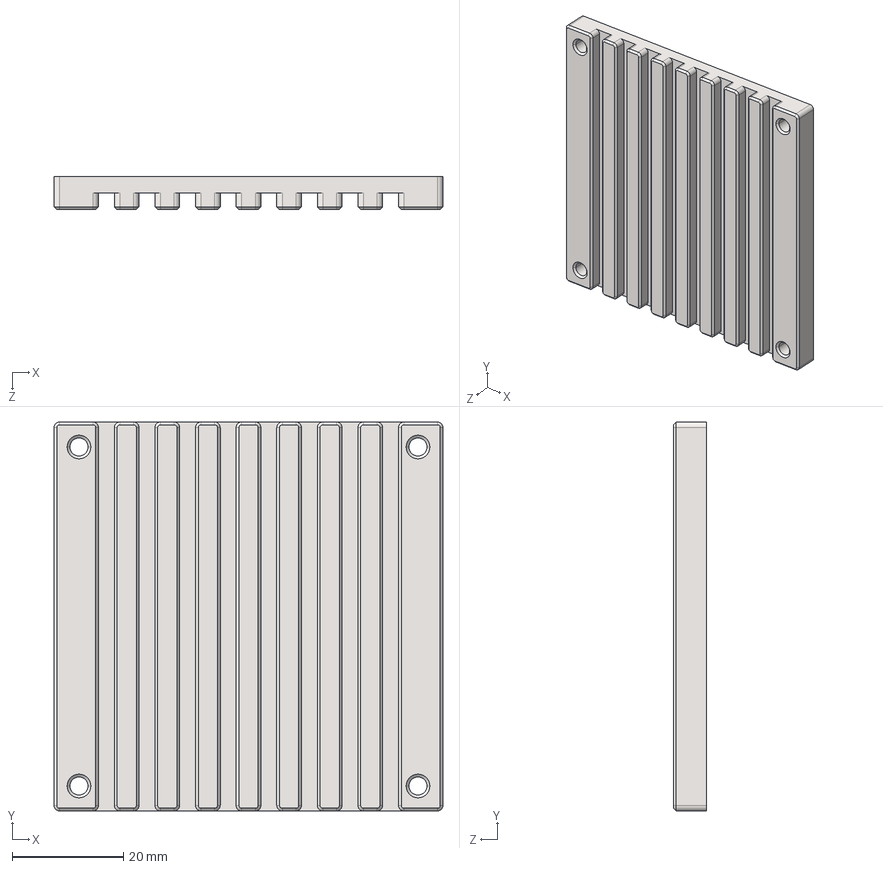
[picture p75: CAD file, 2026-08-21]
Second-Generation-Builds/P4-Wio/STEP/heatsink_external_70x70x3-6mm.STEP
70.0 x 70.0 x 6.00 mm
