ties1887/Mesh-radio-Halow-LoRa/Second-Generation-Builds/CM4-Carrier-Board/models/APCI0085_EasyEDA_C7498138.step

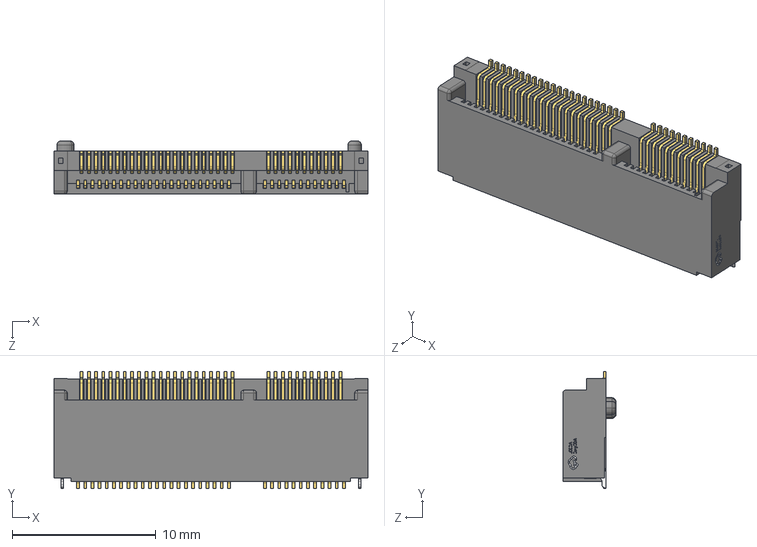
[picture p76: CAD file, 2026-09-19]
Second-Generation-Builds/CM4-Carrier-Board/models/APCI0085_EasyEDA_C7498138.step
21.9 x 8.15 x 3.70 mm
