ties1887/Mesh-radio-Halow-LoRa/Second-Generation-Builds/P4-Wio/STEP/Mpu5 antenna.STEP

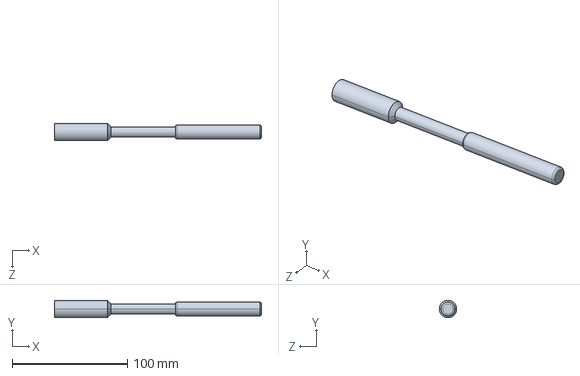
[picture p77: CAD file, 2026-08-21]
Second-Generation-Builds/P4-Wio/STEP/Mpu5 antenna.STEP
180.0 x 15.0 x 15.0 mm
