ties1887/Mesh-radio-Halow-LoRa/Twist-Lock-Battery-Pack/STEP/magnetic pogo pin connector.STEP

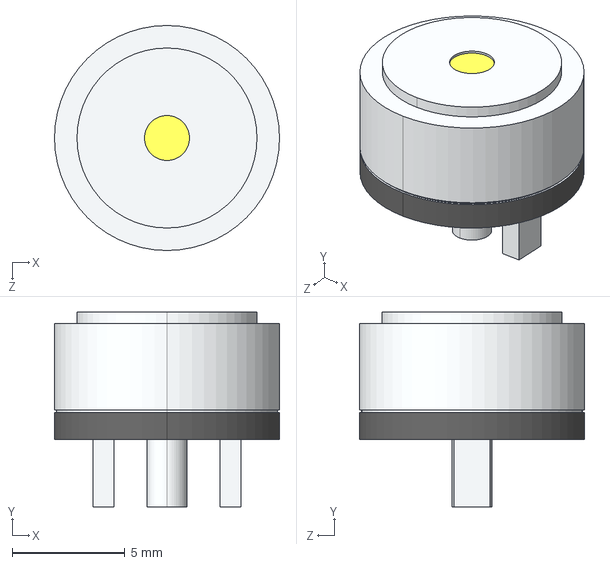
[picture p78: CAD file, 2026-08-21]
Twist-Lock-Battery-Pack/STEP/magnetic pogo pin connector.STEP
10.0 x 8.65 x 10.0 mm
