ties1887/Mesh-radio-Halow-LoRa/First-Generation-Builds/V3_18-6-2026/Solidworks 2025/cooling.SLDPRT

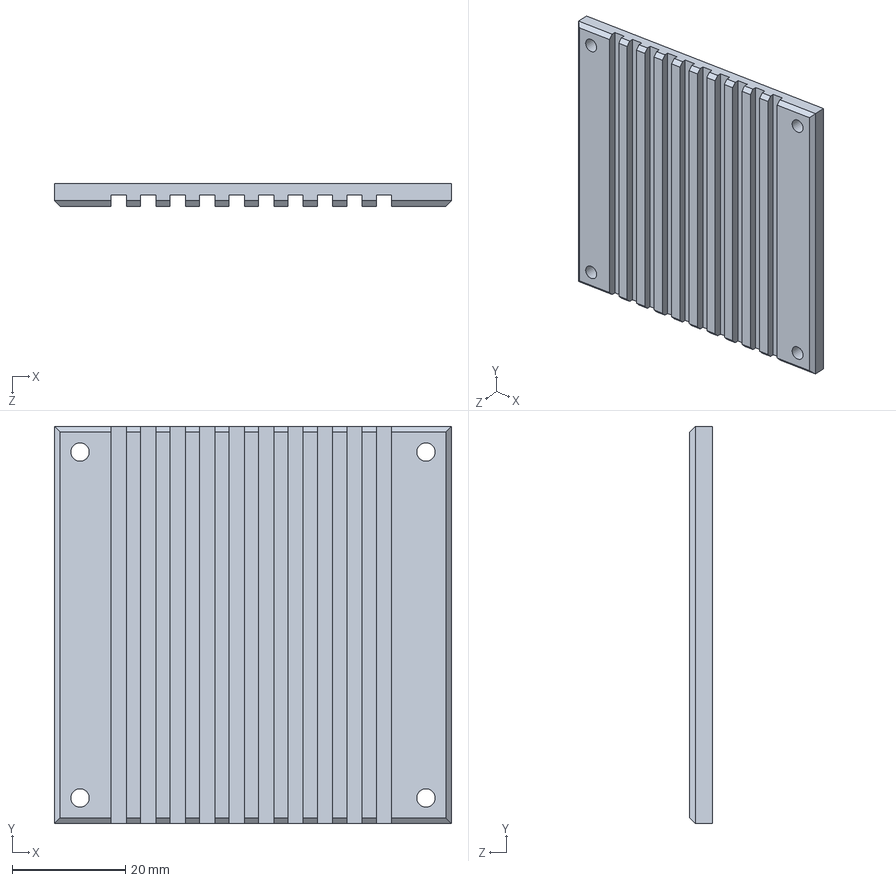
[picture p79: CAD file, 2026-06-18]
First-Generation-Builds/V3_18-6-2026/Solidworks 2025/cooling.SLDPRT
70.0 x 70.0 x 4.00 mm
