ties1887/Mesh-radio-Halow-LoRa/First-Generation-Builds/V3_18-6-2026/STEP/Part1.STEP

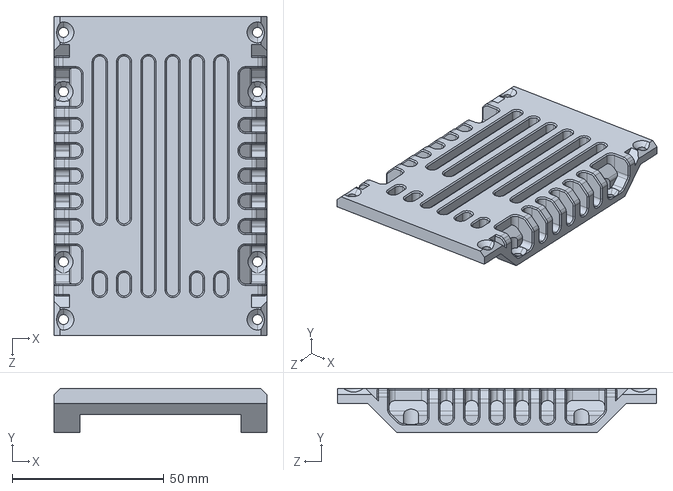
[picture p80: CAD file, 2026-06-18]
First-Generation-Builds/V3_18-6-2026/STEP/Part1.STEP
70.0 x 14.5 x 105.0 mm
