ties1887/Mesh-radio-Halow-LoRa/Second-Generation-Builds/P4-Wio/STEP/gasket_top_cover.STEP

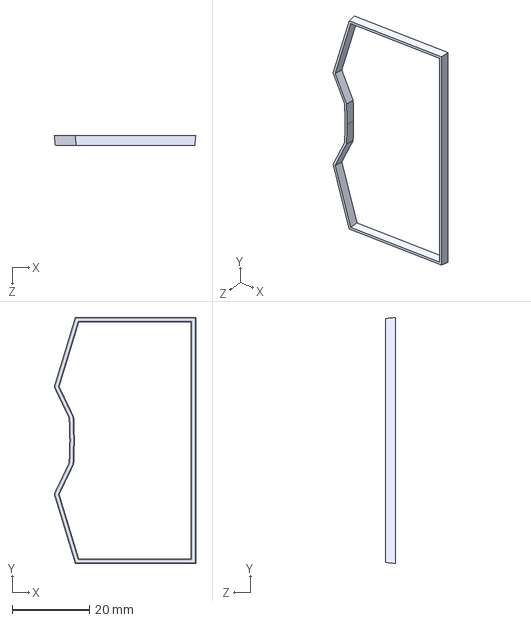
[picture p81: CAD file, 2026-08-21]
Second-Generation-Builds/P4-Wio/STEP/gasket_top_cover.STEP
36.8 x 63.9 x 2.50 mm
