ties1887/Mesh-radio-Halow-LoRa/First-Generation-Builds/V2_30-5-2026/Solidworks 2025/wing part.SLDPRT

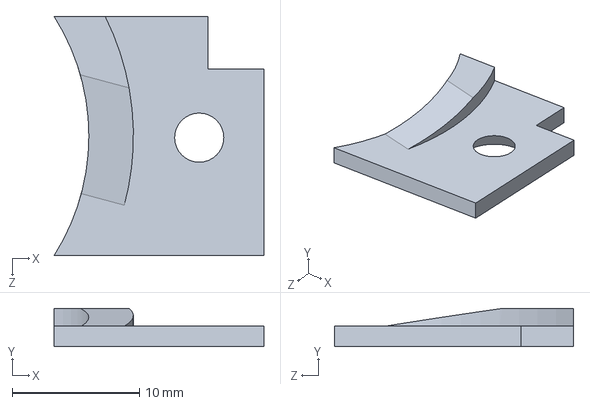
[picture p82: CAD file, 2026-05-30]
First-Generation-Builds/V2_30-5-2026/Solidworks 2025/wing part.SLDPRT
16.5 x 3.00 x 18.8 mm
