ties1887/Mesh-radio-Halow-LoRa/First-Generation-Builds/V2_30-5-2026/STL/Assem2 - TPU gasket for top-1.STL

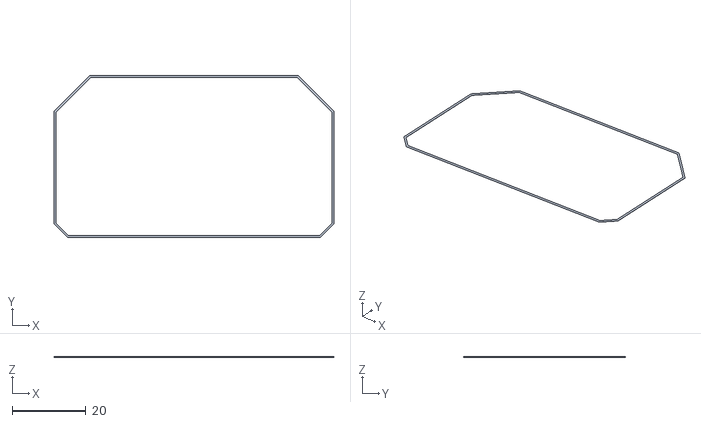
[picture p83: CAD file, 2026-05-31]
First-Generation-Builds/V2_30-5-2026/STL/Assem2 - TPU gasket for top-1.STL
75.8 x 43.8 x 0.24
