ties1887/Mesh-radio-Halow-LoRa/Second-Generation-Builds/P4-Wio/STEP/gasket_heatsink_external.STEP

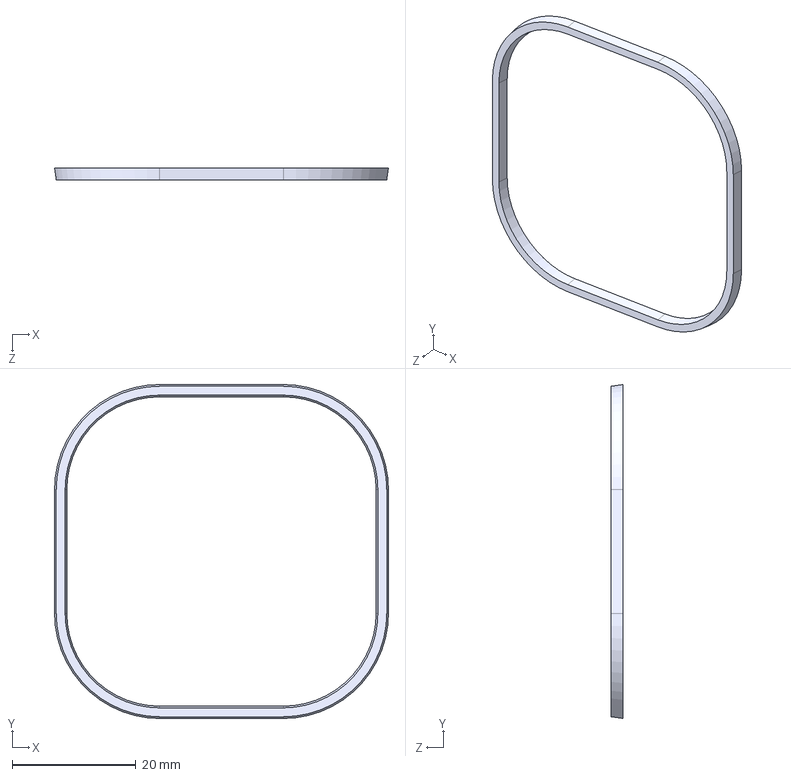
[picture p84: CAD file, 2026-08-21]
Second-Generation-Builds/P4-Wio/STEP/gasket_heatsink_external.STEP
54.0 x 54.0 x 2.00 mm
