ties1887/Mesh-radio-Halow-LoRa/Twist-Lock-Battery-Pack/STEP/Cell_21700.STEP

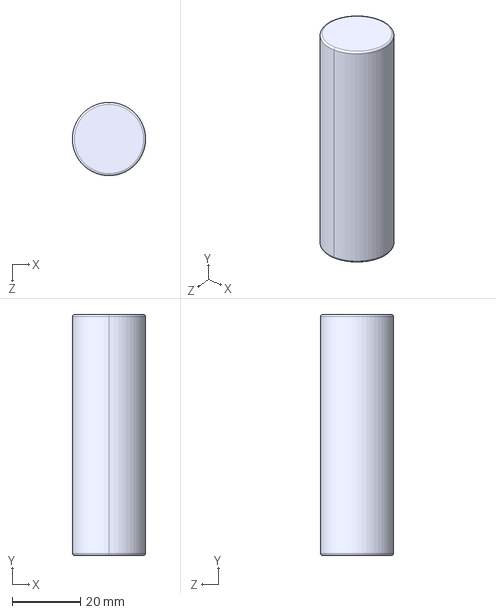
[picture p85: CAD file, 2026-08-21]
Twist-Lock-Battery-Pack/STEP/Cell_21700.STEP
21.5 x 70.7 x 21.5 mm
