ties1887/Mesh-radio-Halow-LoRa/Second-Generation-Builds/P4-Wio/STEP/pololu_buck_converter.STEP

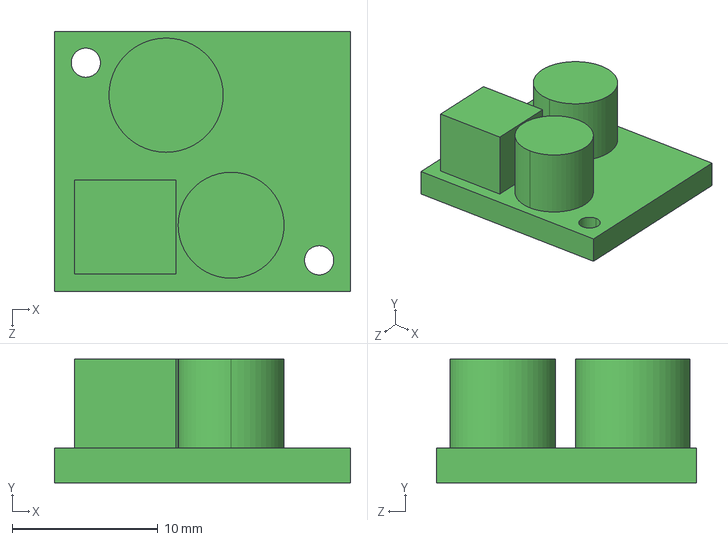
[picture p86: CAD file, 2026-08-21]
Second-Generation-Builds/P4-Wio/STEP/pololu_buck_converter.STEP
20.3 x 8.50 x 17.9 mm
