ties1887/Mesh-radio-Halow-LoRa/Second-Generation-Builds/P4-Wio/STEP/bottom seal.STEP

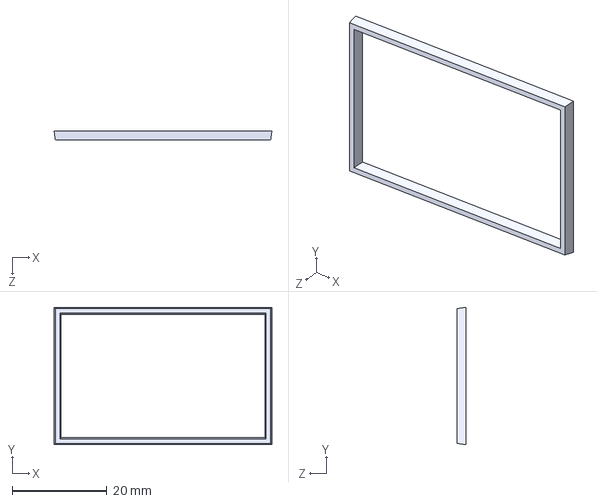
[picture p87: CAD file, 2026-08-21]
Second-Generation-Builds/P4-Wio/STEP/bottom seal.STEP
46.0 x 29.0 x 2.00 mm
