ties1887/Mesh-radio-Halow-LoRa/First-Generation-Builds/V2_30-5-2026/STL/Assem2 - TPU gasket for twist lock part-1.STL

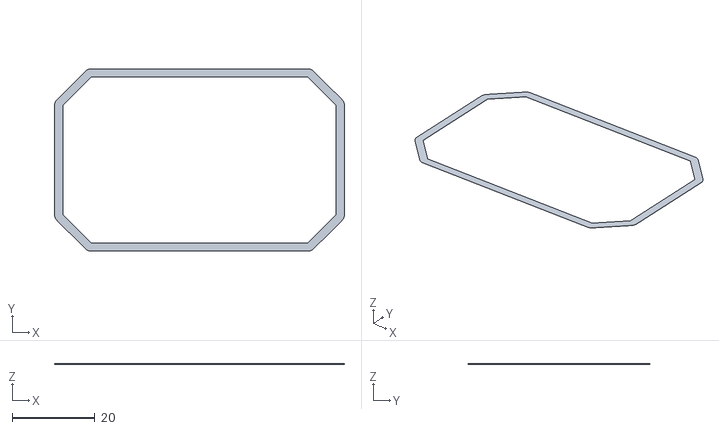
[picture p88: CAD file, 2026-05-31]
First-Generation-Builds/V2_30-5-2026/STL/Assem2 - TPU gasket for twist lock part-1.STL
70.0 x 44.0 x 0.24
