ties1887/Mesh-radio-Halow-LoRa/Second-Generation-Builds/P4-Wio/STEP/gasket_front_cover.STEP

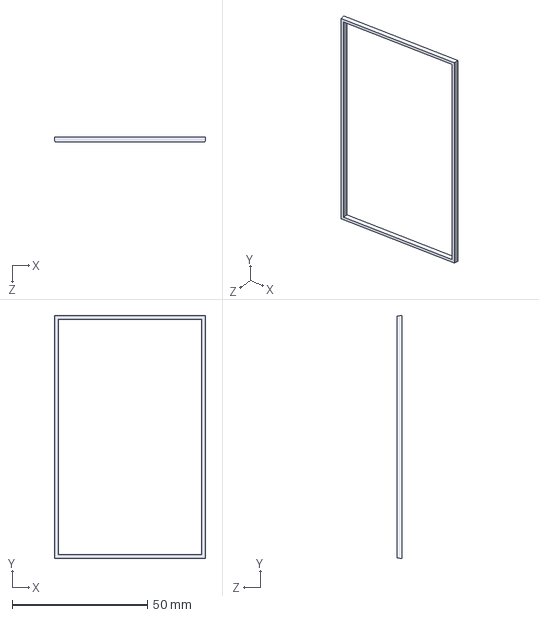
[picture p89: CAD file, 2026-08-21]
Second-Generation-Builds/P4-Wio/STEP/gasket_front_cover.STEP
56.0 x 90.0 x 2.00 mm
